MycroftAI/hardware-mycroft-mark-II/mark-II-Rpi-devkit/Reference Files/Switches/SLIDE.pdf

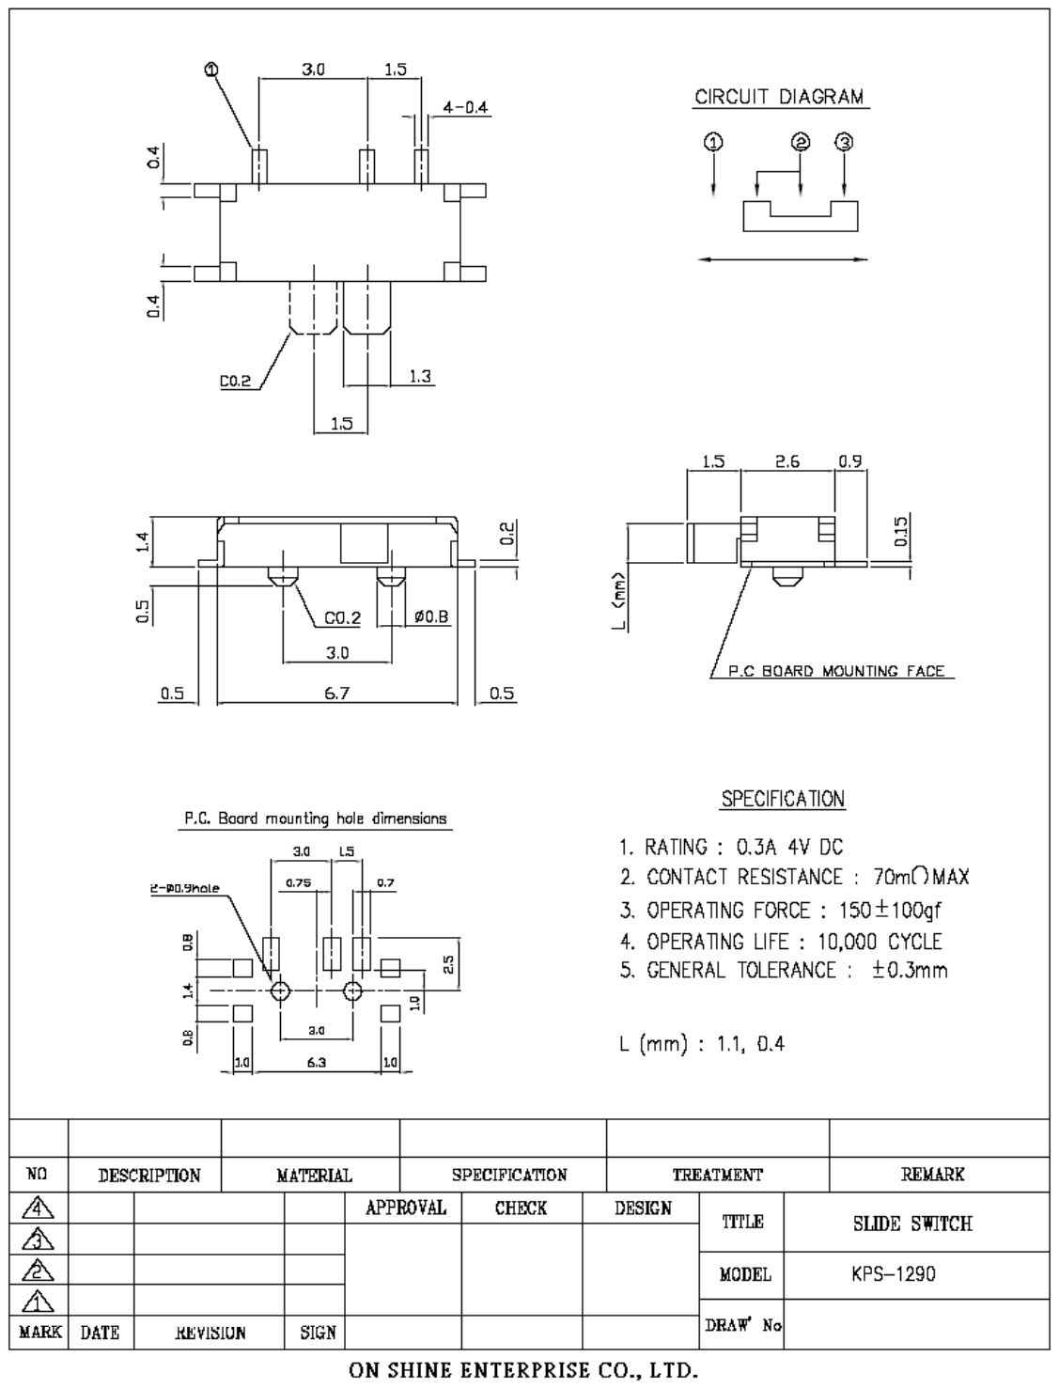
[picture p6: page 1]
