MycroftAI/hardware-mycroft-mark-II/mark-II-production/images/SJ-201-R10-back.png

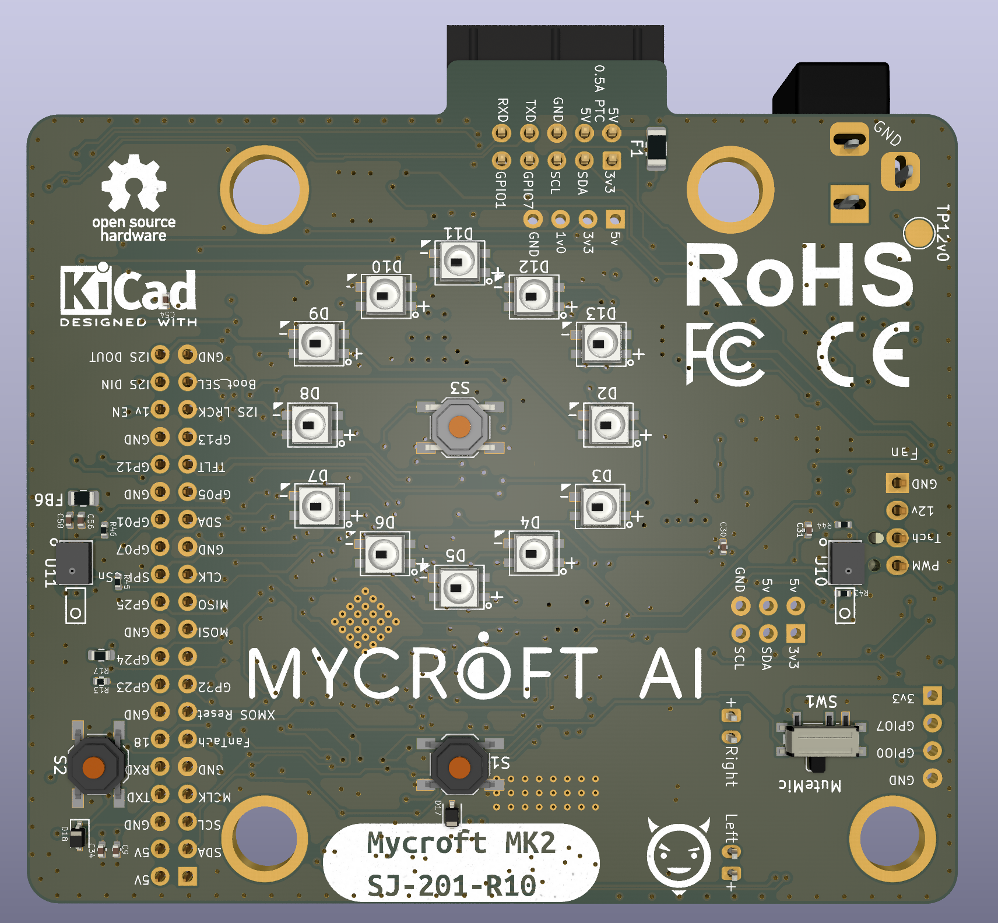
mark-II-production/images/SJ-201-R10-back.png
