MycroftAI/hardware-mycroft-mark-II/mark-II-Rpi-devkit/images/pcb-render-SJ-201-R4v11-front.png

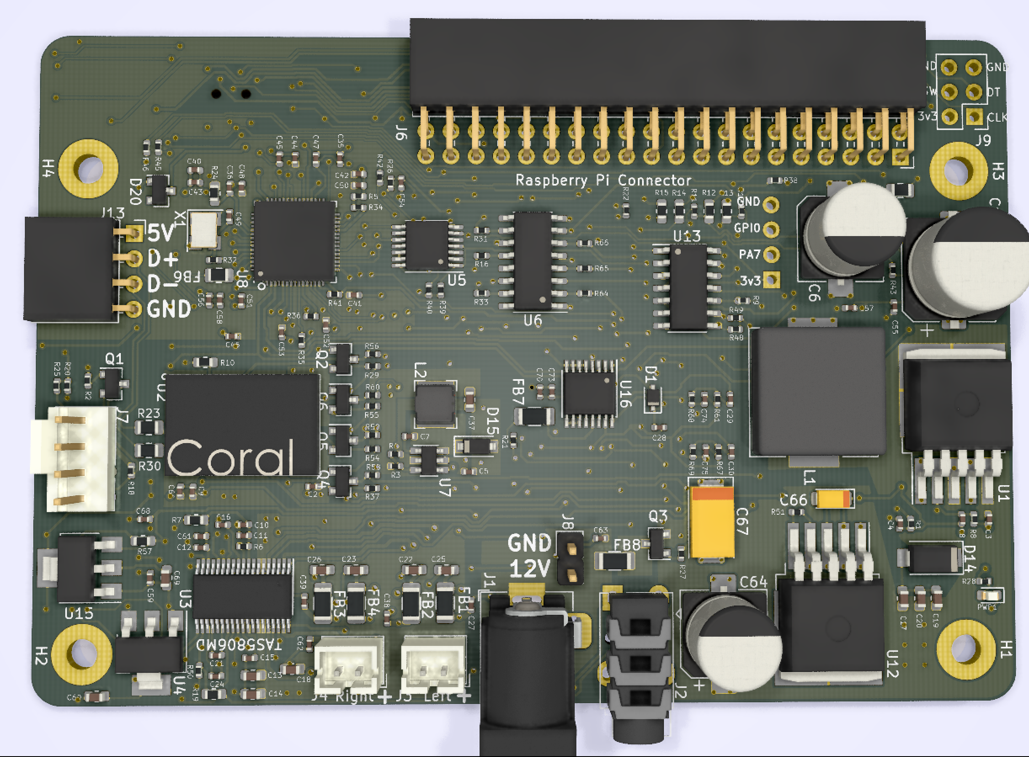
mark-II-Rpi-devkit/images/pcb-render-SJ-201-R4v11-front.png
