MycroftAI/hardware-mycroft-mark-II/mark-II-Rpi-devkit/images/pcb-render-v0.60-front.png

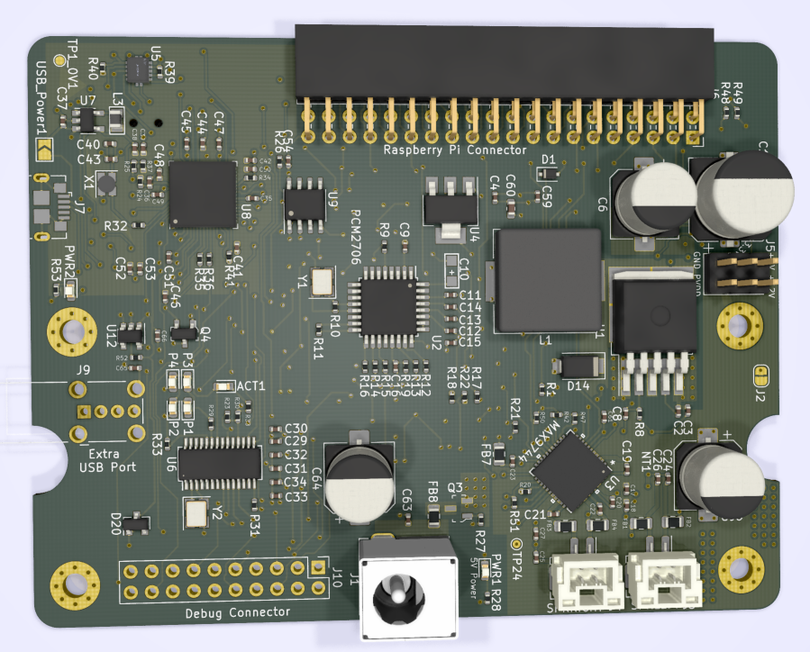
mark-II-Rpi-devkit/images/pcb-render-v0.60-front.png
