MycroftAI/hardware-mycroft-mark-II/mark-II-Rpi-devkit/images/pcb-render-v0.65-front.png

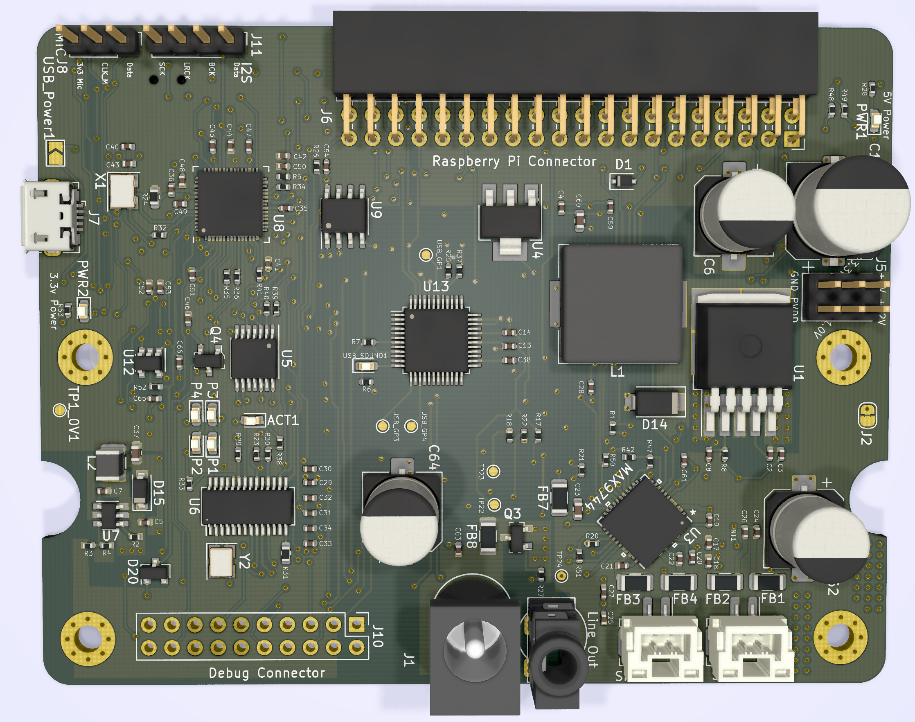
mark-II-Rpi-devkit/images/pcb-render-v0.65-front.png
