MycroftAI/hardware-mycroft-mark-II/mark-II-Rpi-devkit/images/pcb-render-v0.67c-back.png

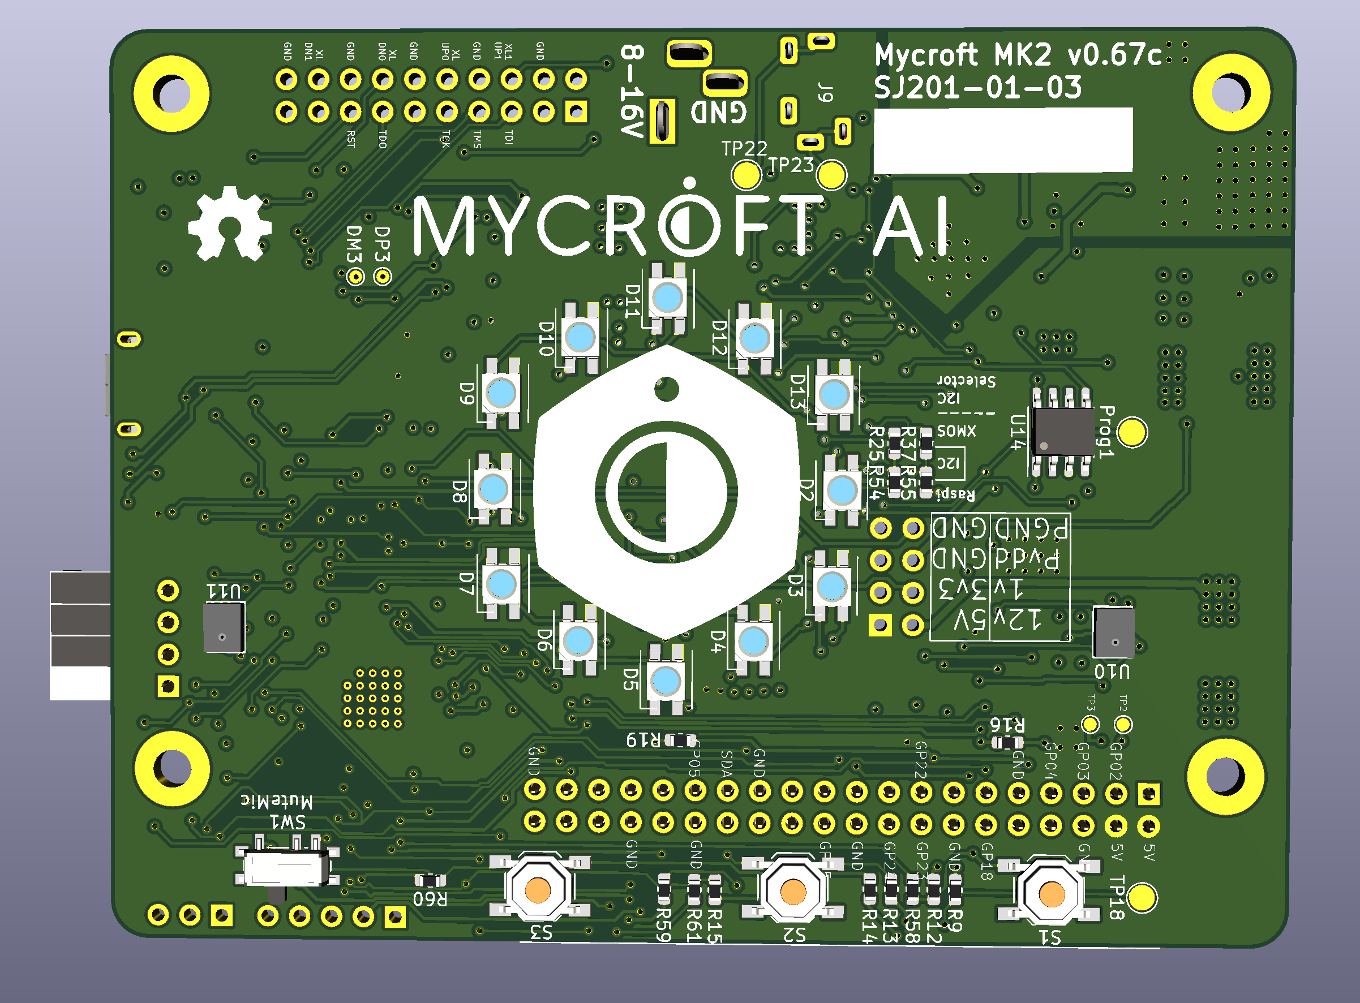
mark-II-Rpi-devkit/images/pcb-render-v0.67c-back.png
