MycroftAI/hardware-mycroft-mark-II/mark-II-Rpi-devkit/images/Sj-201-R4-how it started.png

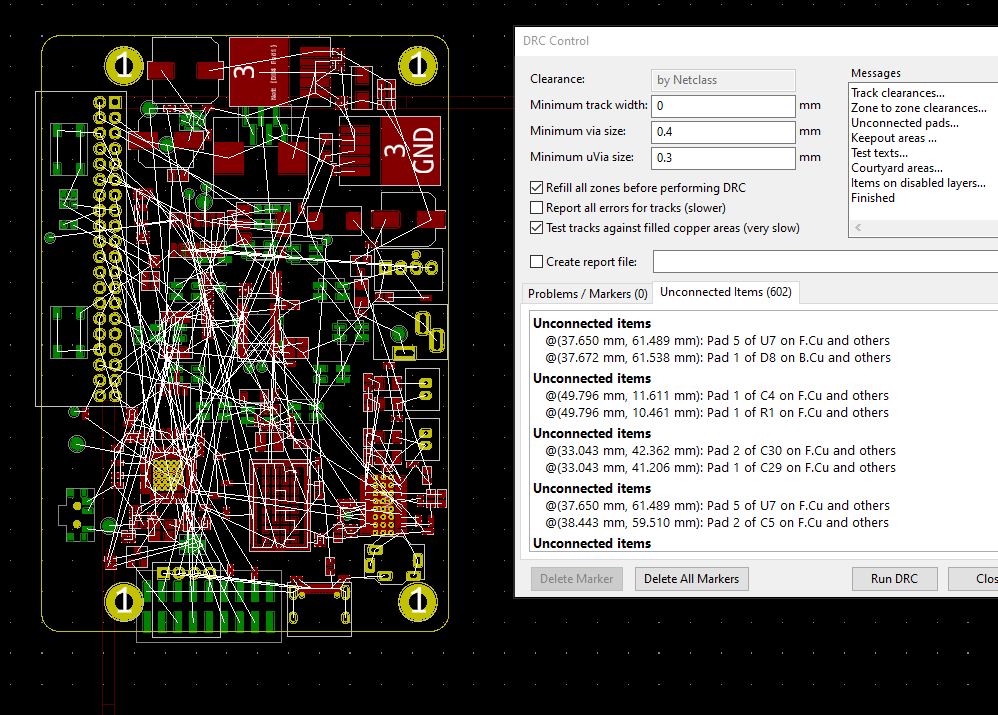
mark-II-Rpi-devkit/images/Sj-201-R4-how it started.png
