MycroftAI/hardware-mycroft-mark-II/mark-II-Rpi-devkit/images/SJ-202-USB-front.png

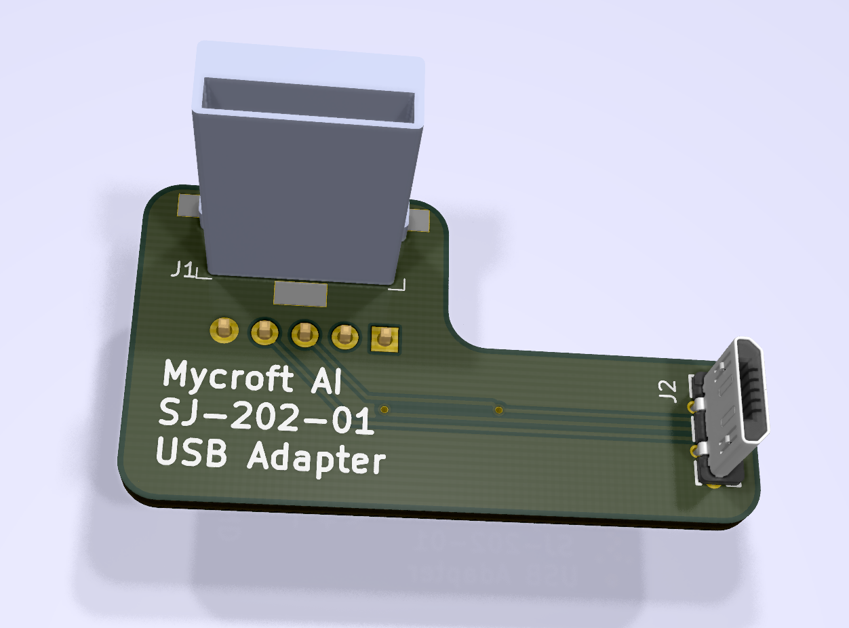
mark-II-Rpi-devkit/images/SJ-202-USB-front.png
