MycroftAI/hardware-mycroft-mark-II/mark-II-rpi-ots/CAD/threaded insert locations/Audio Chamber Back.png

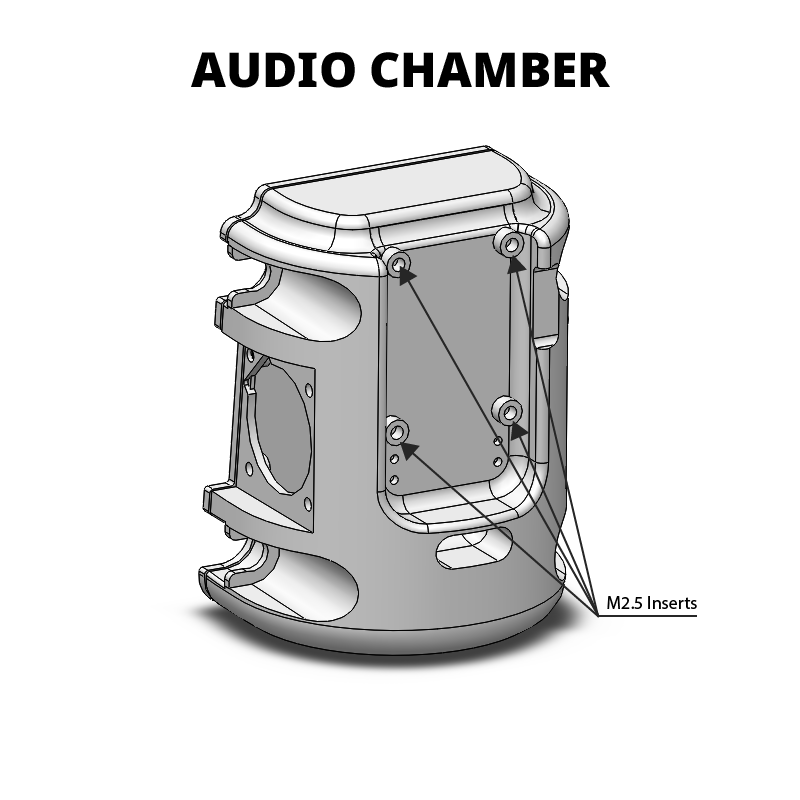
mark-II-rpi-ots/CAD/threaded insert locations/Audio Chamber Back.png
