MycroftAI/hardware-mycroft-mark-II/mark-II-rpi-ots/CAD/threaded insert locations/Audio Chamber Front.png

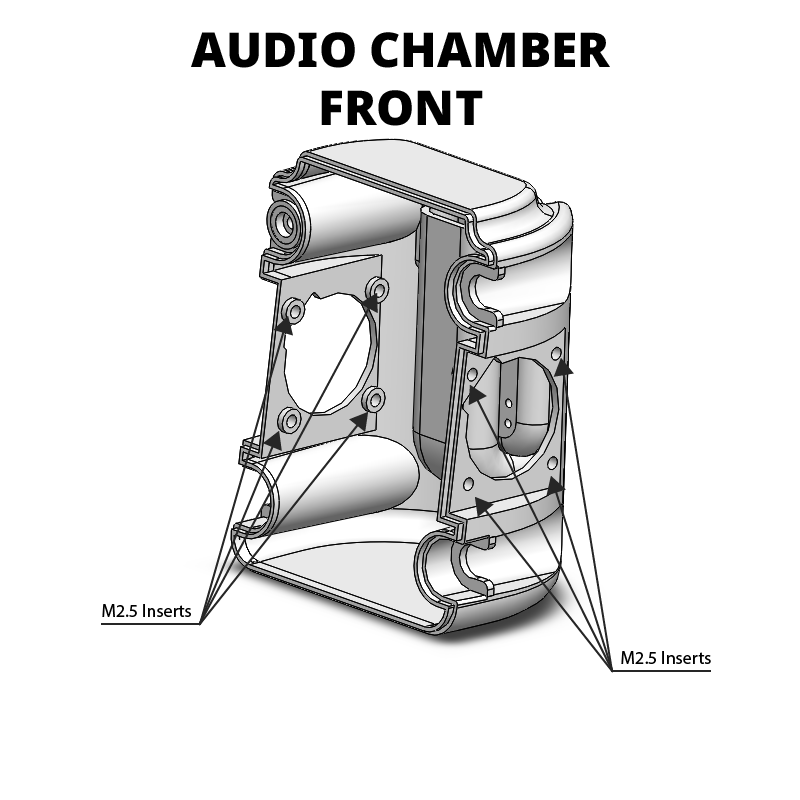
mark-II-rpi-ots/CAD/threaded insert locations/Audio Chamber Front.png
