MycroftAI/hardware-mycroft-mark-II/mark-II-rpi-ots/CAD/threaded insert locations/Base.png

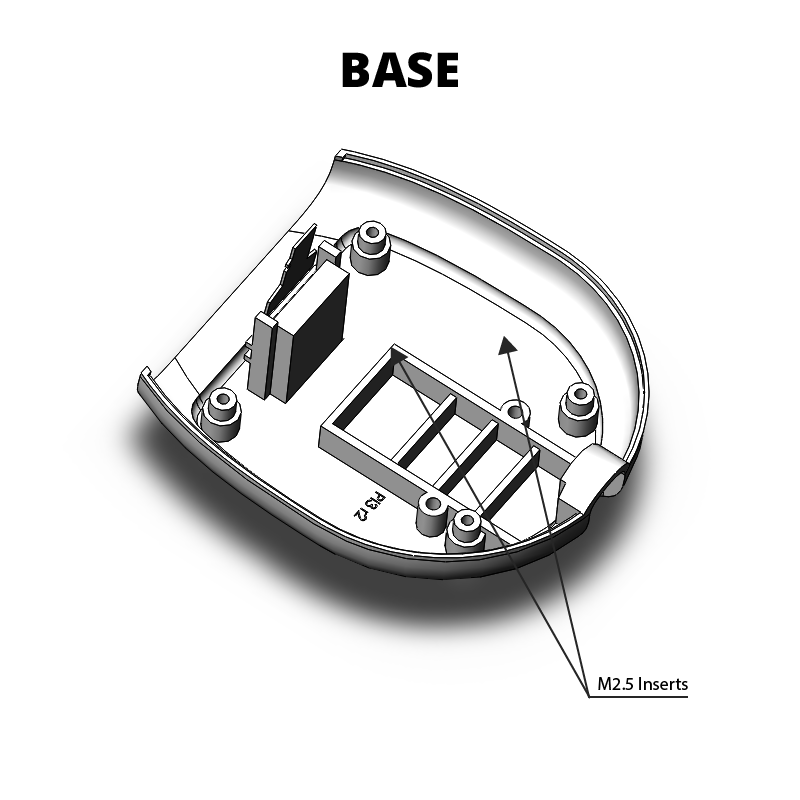
mark-II-rpi-ots/CAD/threaded insert locations/Base.png
