MycroftAI/hardware-mycroft-mark-II/mark-II-rpi-ots/CAD/threaded insert locations/Front.png

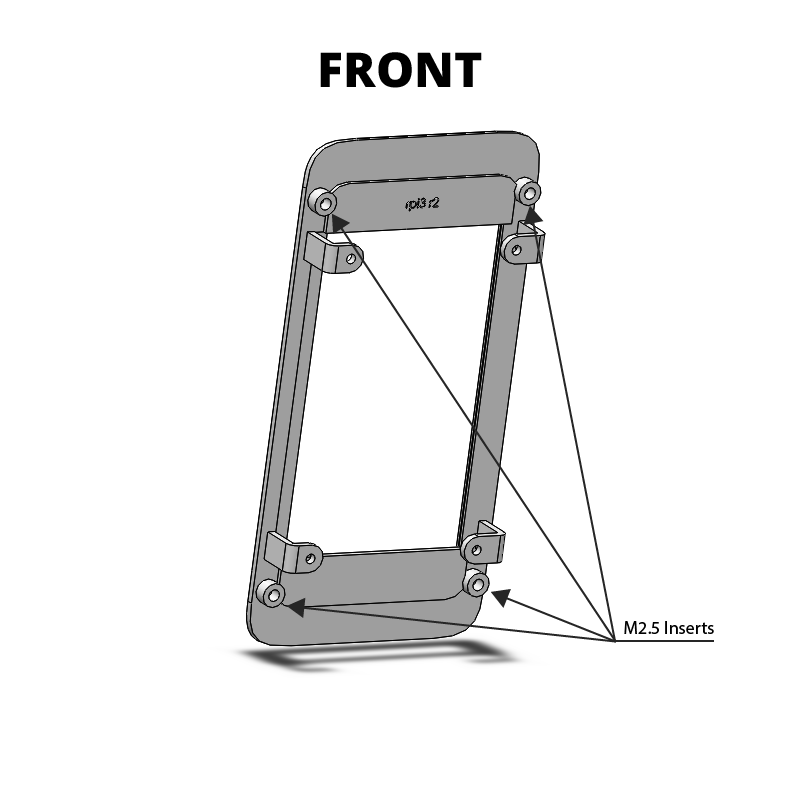
mark-II-rpi-ots/CAD/threaded insert locations/Front.png
