MycroftAI/hardware-mycroft-mark-II/mark-II-rpi-ots/CAD/threaded insert locations/Top-2.png

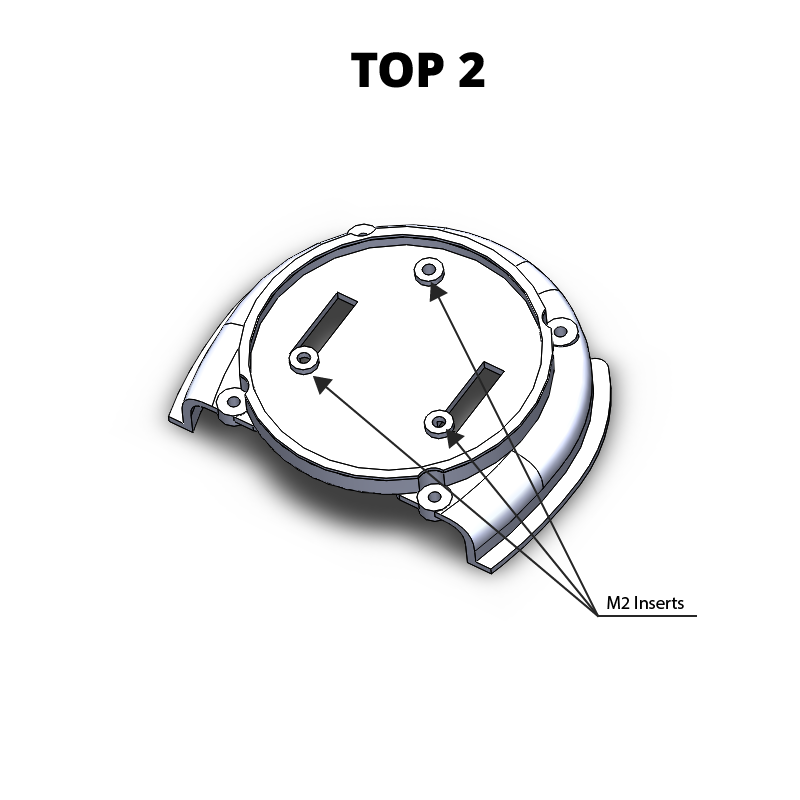
mark-II-rpi-ots/CAD/threaded insert locations/Top-2.png
