MycroftAI/hardware-mycroft-mark-II/mark-II-rpi-ots/CAD/threaded insert locations/Top.png

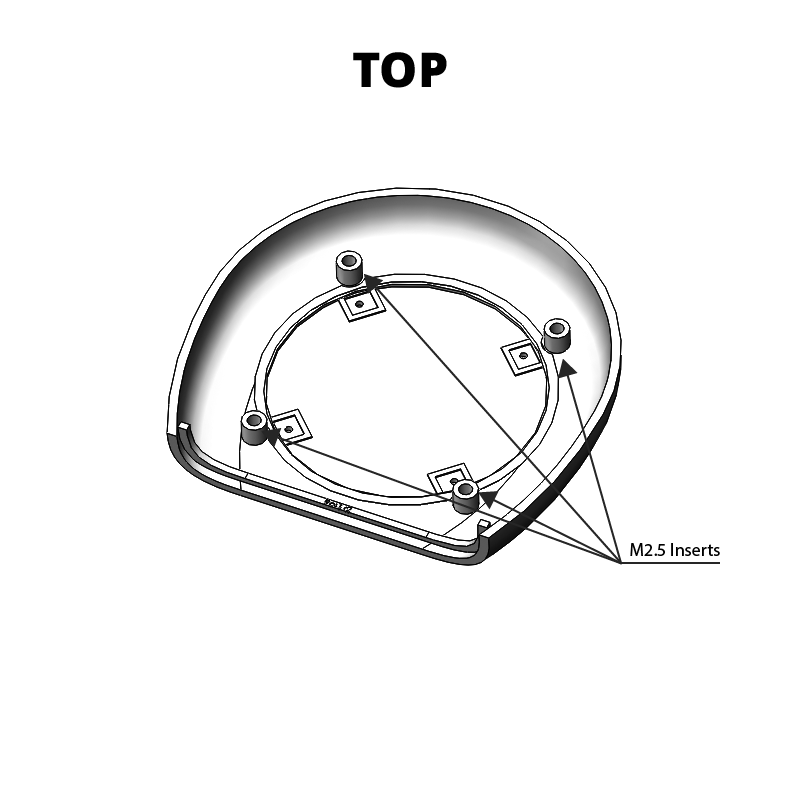
mark-II-rpi-ots/CAD/threaded insert locations/Top.png
