MycroftAI/hardware-mycroft-mark-II/mark-II-Rpi-devkit/Mechanical CAD/SJ240/MKII Camera Shutter 3 r9.stl

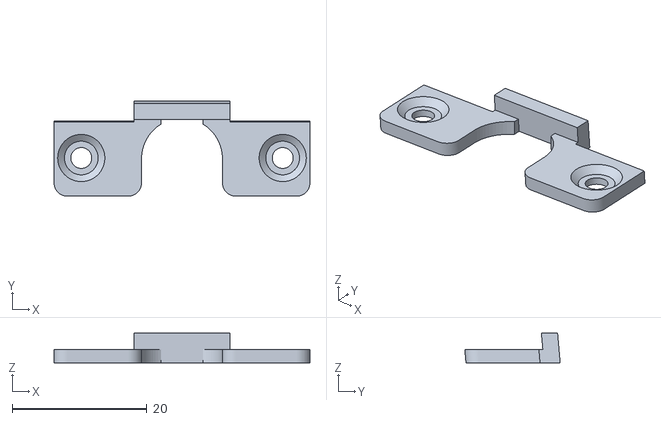
[picture p50: CAD file, 2021-03-14]
mark-II-Rpi-devkit/Mechanical CAD/SJ240/MKII Camera Shutter 3 r9.stl
38.0 x 14.2 x 4.41
