MycroftAI/hardware-mycroft-mark-II/mark-II-rpi-ots/CAD/STL/MIIr_AC_front_pi3_r2.1.STL

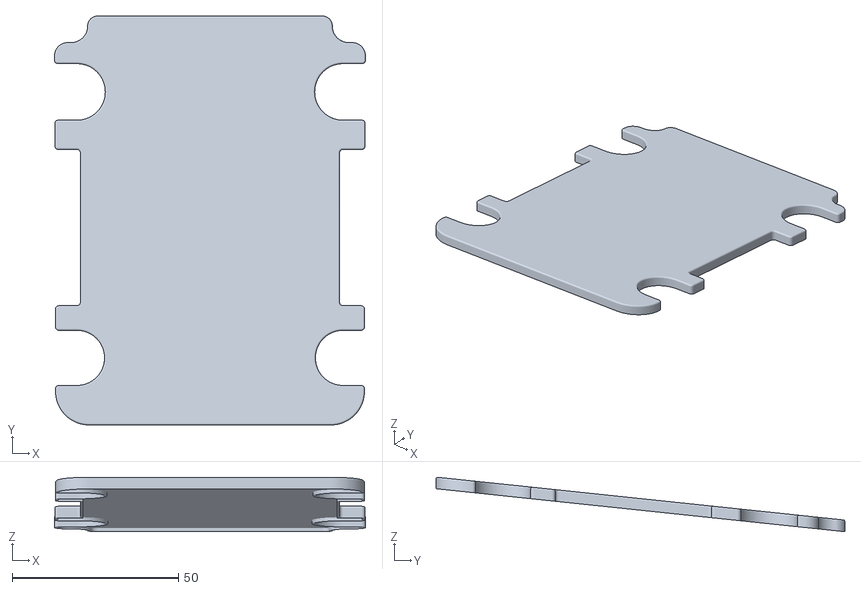
[picture p51: CAD file, 2020-01-30]
mark-II-rpi-ots/CAD/STL/MIIr_AC_front_pi3_r2.1.STL
93.5 x 123.0 x 16.4
