MycroftAI/hardware-mycroft-mark-II/mark-II-Rpi-devkit/Mechanical CAD/SJ240/MKII Camera Shutter 2 r9.stl

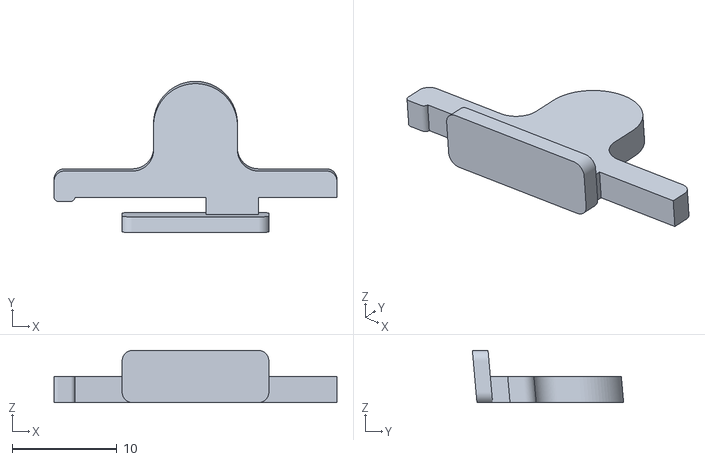
[picture p52: CAD file, 2021-03-14]
mark-II-Rpi-devkit/Mechanical CAD/SJ240/MKII Camera Shutter 2 r9.stl
27.0 x 14.4 x 4.98
