MycroftAI/hardware-mycroft-mark-II/mark-II-rpi-ots/CAD/STL/MIIr_base_pi3_r2.STL

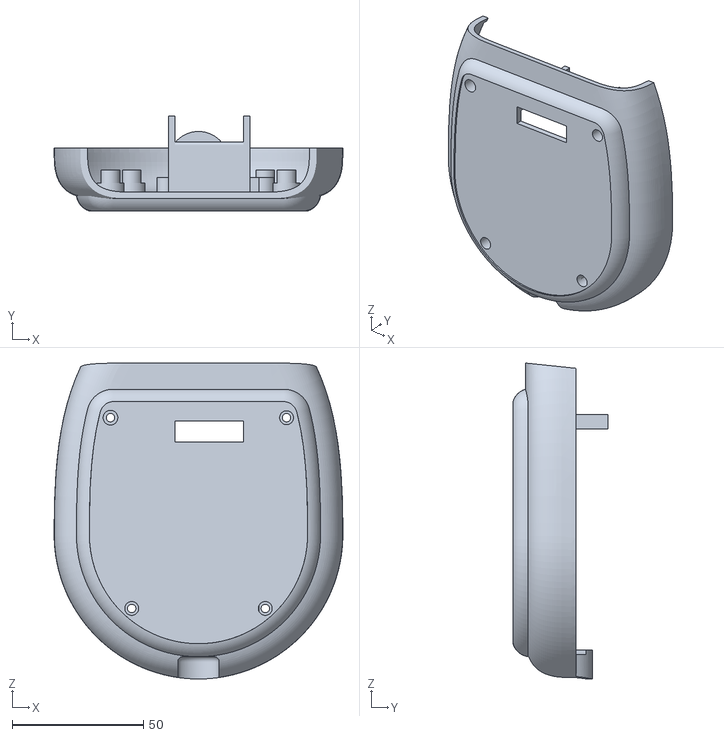
[picture p53: CAD file, 2020-01-30]
mark-II-rpi-ots/CAD/STL/MIIr_base_pi3_r2.STL
110.0 x 36.2 x 120.4
