MycroftAI/hardware-mycroft-mark-II/mark-II-Rpi-devkit/Mechanical CAD/SJ240/MKII Camera Shutter 1 r9.stl

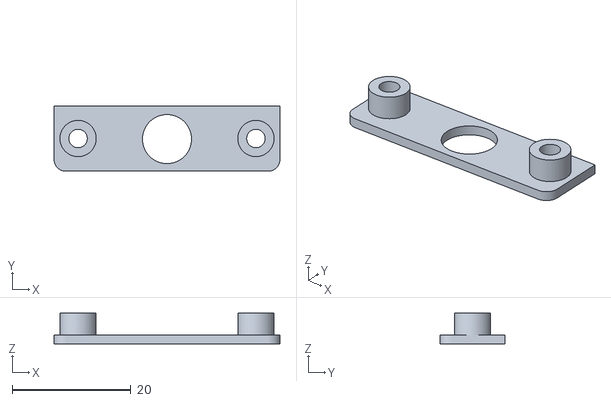
[picture p54: CAD file, 2021-03-14]
mark-II-Rpi-devkit/Mechanical CAD/SJ240/MKII Camera Shutter 1 r9.stl
38.0 x 11.0 x 5.14
