MycroftAI/hardware-mycroft-mark-II/mark-II-rpi-ots/CAD/STL/MIIr_back_bosses_pi3_r2.STL

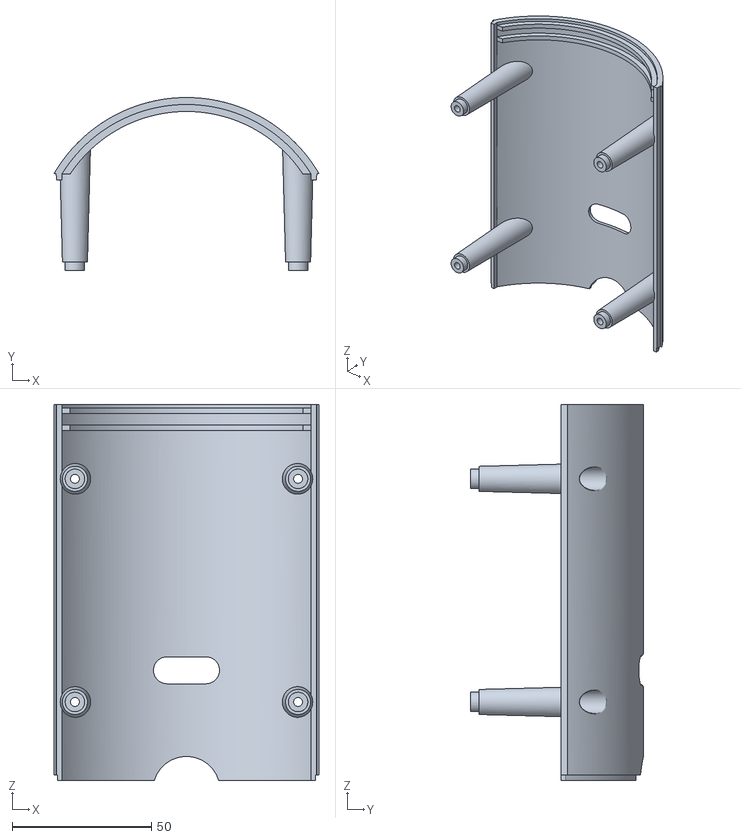
[picture p55: CAD file, 2020-01-20]
mark-II-rpi-ots/CAD/STL/MIIr_back_bosses_pi3_r2.STL
95.0 x 62.0 x 134.8
