MycroftAI/hardware-mycroft-mark-II/mark-II-Rpi-devkit/Mechanical CAD/SJ240/MKII switch r9.stl

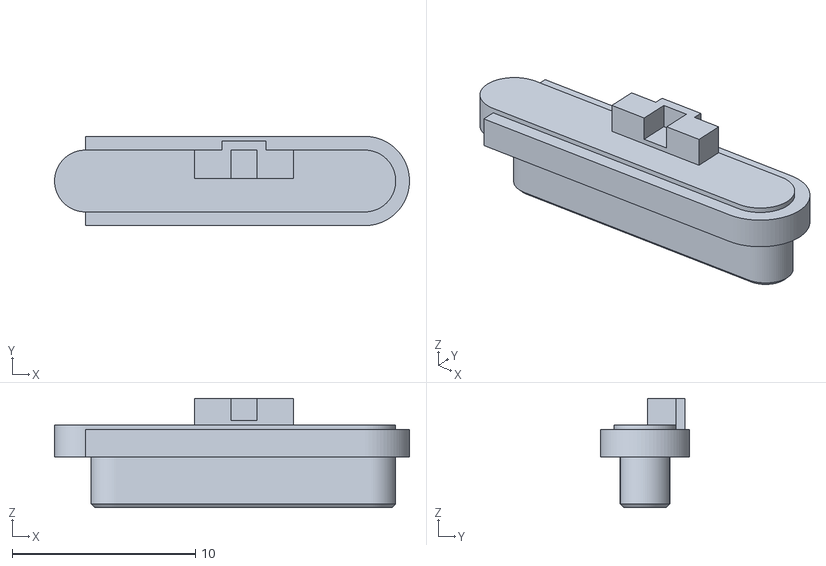
[picture p56: CAD file, 2021-03-14]
mark-II-Rpi-devkit/Mechanical CAD/SJ240/MKII switch r9.stl
19.4 x 4.87 x 5.96
