MycroftAI/hardware-mycroft-mark-II/mark-II-rpi-ots/CAD/STL/MIIr_front_plate_pi3_r2.STL

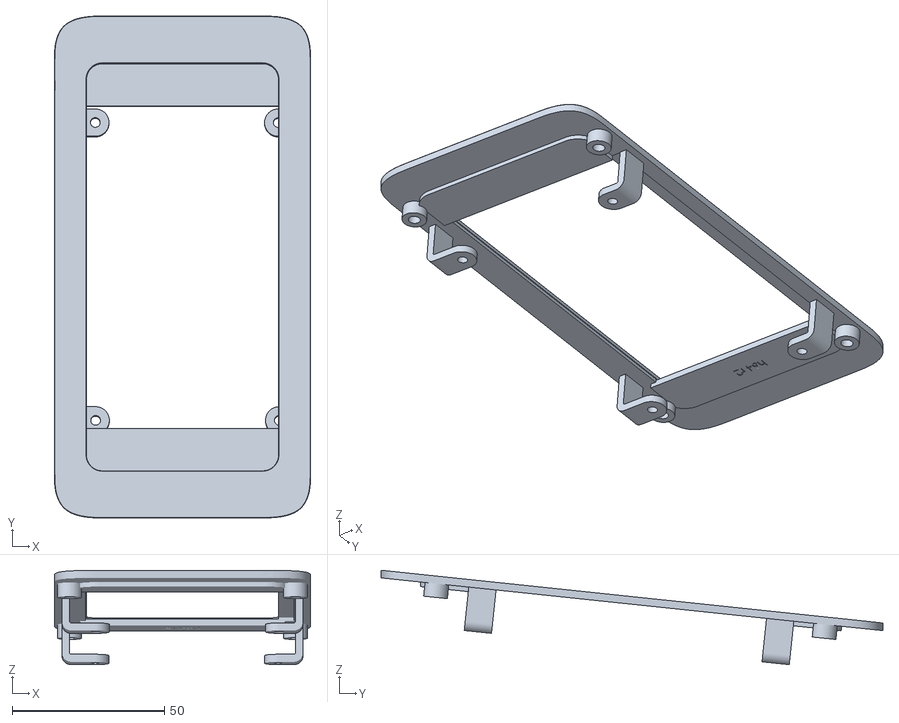
[picture p57: CAD file, 2020-01-20]
mark-II-rpi-ots/CAD/STL/MIIr_front_plate_pi3_r2.STL
84.0 x 164.6 x 30.9
