MycroftAI/hardware-mycroft-mark-II/mark-II-Rpi-devkit/Mechanical CAD/SJ240/MKII buttons r9.1.STL

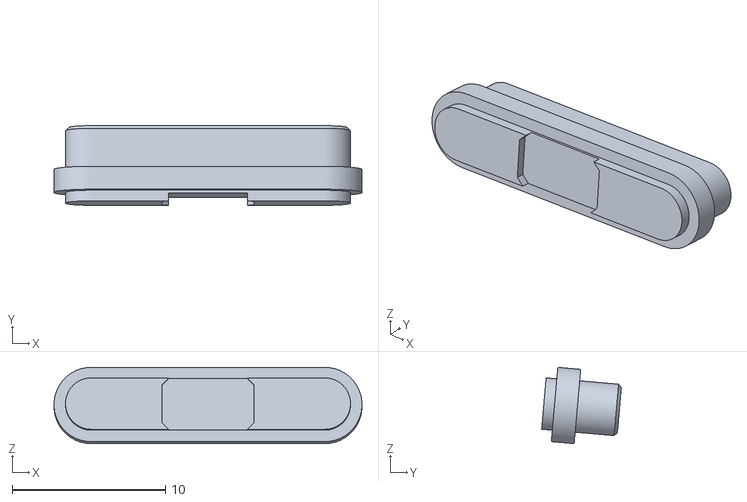
[picture p58: CAD file, 2021-03-14]
mark-II-Rpi-devkit/Mechanical CAD/SJ240/MKII buttons r9.1.STL
20.1 x 5.21 x 4.98
