MycroftAI/hardware-mycroft-mark-II/mark-II-Rpi-devkit/Mechanical CAD/SJ240/MKII Display Bezel R9.stl

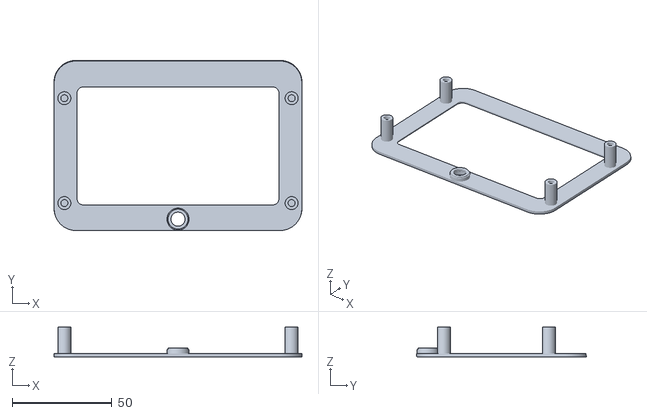
[picture p61: CAD file, 2021-03-12]
mark-II-Rpi-devkit/Mechanical CAD/SJ240/MKII Display Bezel R9.stl
124.1 x 85.1 x 14.9
