MycroftAI/hardware-mycroft-mark-II/mark-II-Rpi-devkit/Mechanical CAD/SJ240/MKII Display Housing r9.stl

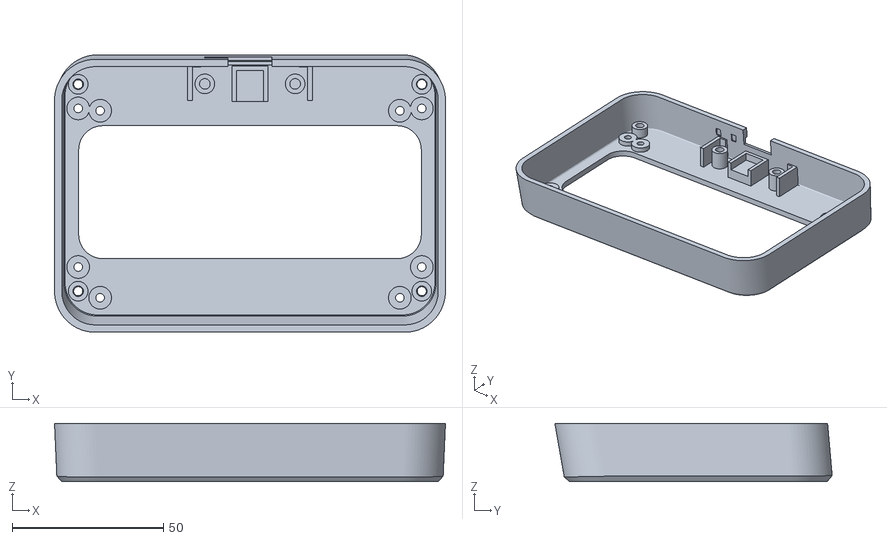
[picture p62: CAD file, 2021-03-12]
mark-II-Rpi-devkit/Mechanical CAD/SJ240/MKII Display Housing r9.stl
129.4 x 91.8 x 19.3
