MycroftAI/hardware-mycroft-mark-II/mark-II-Rpi-devkit/Mechanical CAD/SJ240/MKII Back r9.stl

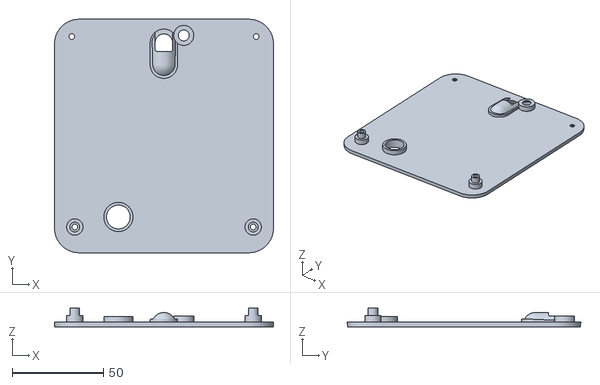
[picture p63: CAD file, 2021-03-12]
mark-II-Rpi-devkit/Mechanical CAD/SJ240/MKII Back r9.stl
120.0 x 128.0 x 10.2
