MycroftAI/hardware-mycroft-mark-II/mark-II-Rpi-devkit/Mechanical CAD/SJ240/MKII Grill r9.stl

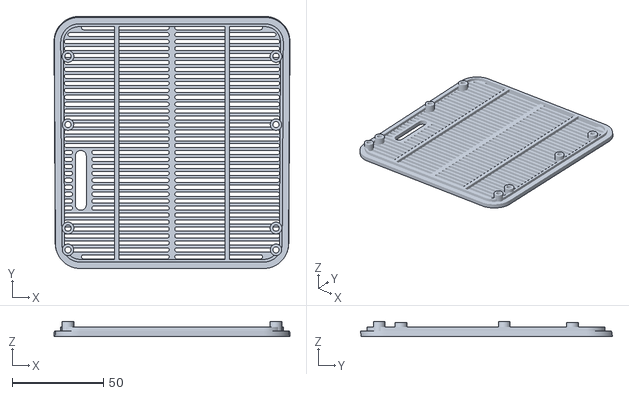
[picture p64: CAD file, 2021-03-12]
mark-II-Rpi-devkit/Mechanical CAD/SJ240/MKII Grill r9.stl
129.0 x 137.8 x 8.00
