MycroftAI/hardware-mycroft-mark-II/mark-II-Rpi-devkit/Mechanical CAD/SJ240/MKII Audio Chamber r9.stl

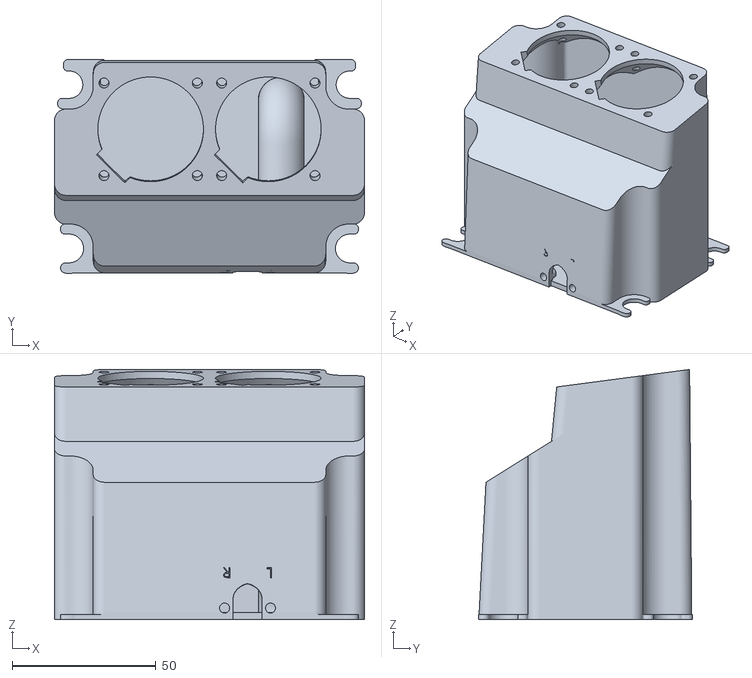
[picture p65: CAD file, 2021-03-12]
mark-II-Rpi-devkit/Mechanical CAD/SJ240/MKII Audio Chamber r9.stl
108.0 x 74.5 x 87.1
