MycroftAI/hardware-mycroft-mark-II/mark-II-production/assembly-instructions/images/display02.jpeg

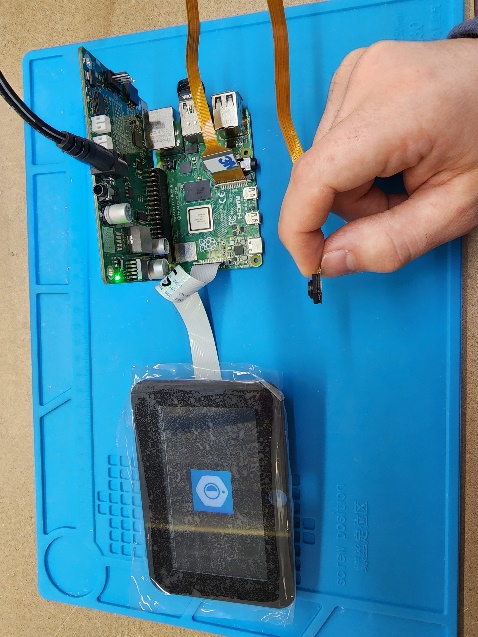
mark-II-production/assembly-instructions/images/display02.jpeg
