MycroftAI/hardware-mycroft-mark-II/mark-II-Rpi-devkit/images/JLC 0.65a-front assembly.png

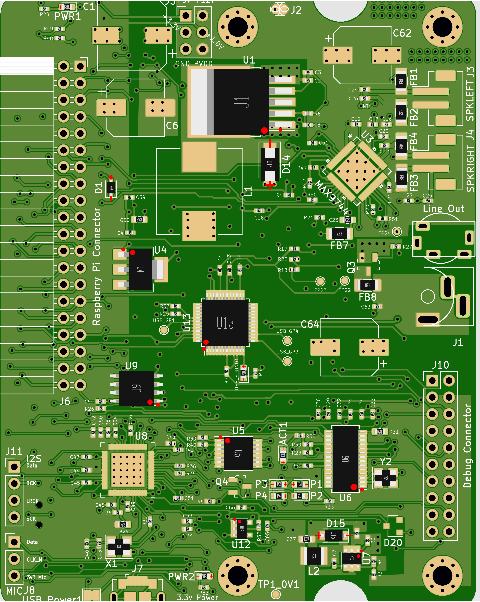
mark-II-Rpi-devkit/images/JLC 0.65a-front assembly.png
