MycroftAI/hardware-mycroft-mark-II/mark-II-production/AudioAmp.kicad_sch

## KiCad design mark-II-production/AudioAmp.kicad_sch (2022-10-22)

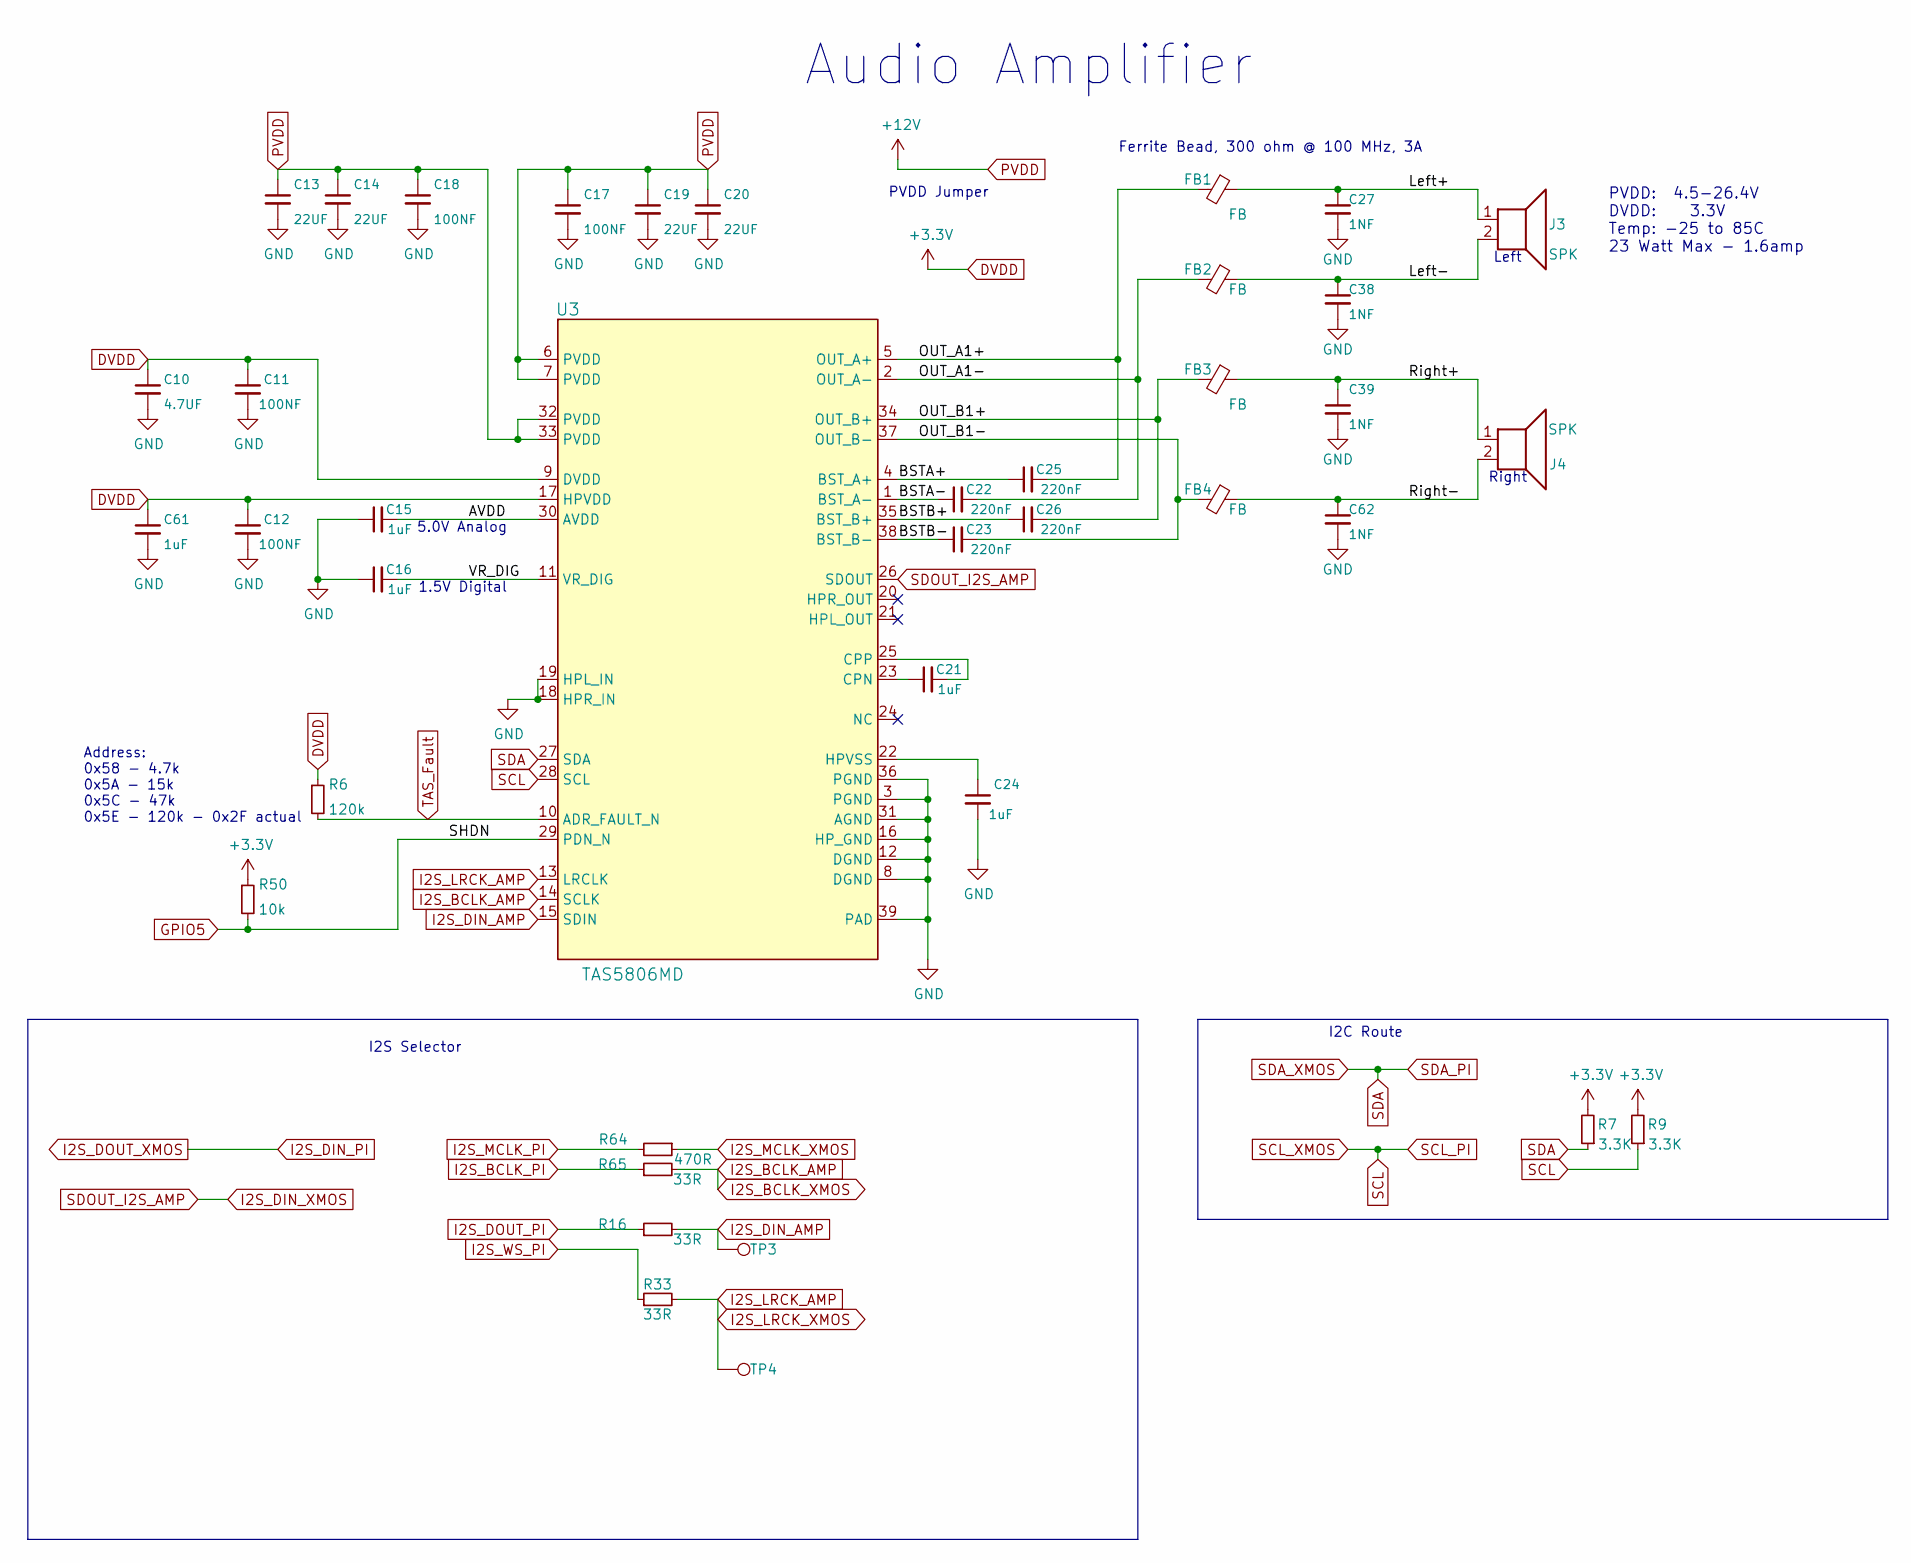
[picture p143: schematic AudioAmp.kicad_sch]

Parts:
C10: 4.7UF; C_0402_1005Metric; MPN CL05A475MP5NRNC; LCSC C23733
C11, C12: 100NF; C_0402_1005Metric; MPN CC0402KRX7R8BB104; LCSC C1525
C13, C14, C19, C20: 22UF; C_0603_1608Metric; MPN CL10A226MQ8NRNC; LCSC C59461
C15, C16, C21, C24, C61: 1uF; C_0402_1005Metric; MPN CL05A105KA5NQNC; LCSC C52923
C17, C18: 100NF; C_0603_1608Metric; MPN CC0603KRX7R9BB104; LCSC C14663
C22, C23, C25, C26: 220nF; C_0603_1608Metric; MPN CL10B224KA8NNNC; LCSC C21120
C27, C38, C39, C62: 1NF; C_0402_1005Metric; MPN 0402B102K500NT; LCSC C1523
FB1, FB2, FB3, FB4: FB; R_1206_3216Metric; MPN MLB3216-301P3A(f); LCSC C29107
J3, J4: SPK; JST_PH_B2B-PH-K_1x02_P2.00mm_Vertical; MPN B2B-PH-K-S(LF)(SN); LCSC C131337
R6: 120k; R_0402_1005Metric; MPN 0402WGF1203TCE; LCSC C25750
R7, R9: 3.3K; R_0402_1005Metric; MPN 0402WGF3301TCE; LCSC C25890
R16, R33, R65: 33R; R_0402_1005Metric; MPN 0402WGF330JTCE; LCSC C25105
R50: 10k; R_0402_1005Metric; MPN RC0402FR-0710KL; LCSC C25744
R64: 470R; R_0603_1608Metric; MPN 0603WAF4700T5E; LCSC C23179
TP3, TP4: TestPoint; TestPoint_Pad_D1.0mm; MPN DNP
U3: TAS5806MD; TAS5806MDDCPR; MPN TAS5806MDDCPR

Connections:
+3.3V: C10.1, C11.1, C12.1, C61.1, R6.1, R7.2, R9.2, R50.1, U3.9 (DVDD), U3.17 (HPVDD)
+12V: C13.1, C14.1, C17.1, C18.1, C19.1, C20.1, U3.6 (PVDD), U3.7 (PVDD), U3.32 (PVDD), U3.33 (PVDD)
AVDD: C15.2, U3.30 (AVDD)
BSTA+: C25.1, U3.4 (BST_A+)
BSTA-: C22.1, U3.1 (BST_A-)
BSTB+: C26.1, U3.35 (BST_B+)
BSTB-: C23.1, U3.38 (BST_B-)
GND: C10.2, C11.2, C12.2, C13.2, C14.2, C15.1, C16.1, C17.2, C18.2, C19.2, C20.2, C24.2, C27.2, C38.2, C39.2, C61.2, C62.2, U3.3 (PGND), U3.8 (DGND), U3.12 (DGND), U3.16 (HP_GND), U3.18 (HPR_IN), U3.19 (HPL_IN), U3.31 (AGND), U3.36 (PGND), U3.39 (PAD)
GPIO5: R50.2, U3.29 (PDN_N)
I2S_BCLK_AMP: R65.2, U3.14 (SCLK)
I2S_BCLK_PI: R65.1
I2S_DIN_AMP: R16.2, TP3.1, U3.15 (SDIN)
I2S_DIN_XMOS: U3.26 (SDOUT)
I2S_DOUT_PI: R16.1
I2S_LRCK_AMP: R33.2, TP4.1, U3.13 (LRCLK)
I2S_MCLK_PI: R64.2
I2S_MCLK_XMOS: R64.1
I2S_WS_PI: R33.1
Left+: C27.1, FB1.1, J3.1
Left-: C38.1, FB2.1, J3.2
unnamed: C21.1, U3.23 (CPN)
unnamed: C21.2, U3.25 (CPP)
unnamed: C24.1, U3.22 (HPVSS)
OUT_A1+: C25.2, FB1.2, U3.5 (OUT_A+)
OUT_A1-: C22.2, FB2.2, U3.2 (OUT_A-)
OUT_B1+: C26.2, FB3.2, U3.34 (OUT_B+)
OUT_B1-: C23.2, FB4.2, U3.37 (OUT_B-)
Right+: C39.1, FB3.1, J4.1
Right-: C62.1, FB4.1, J4.2
SCL: R9.1, U3.28 (SCL)
SDA: R7.1, U3.27 (SDA)
TAS_Fault: R6.2, U3.10 (ADR_FAULT_N)
VR_DIG: C16.2, U3.11 (VR_DIG)

Notes on the sheet:
1.5V Digital
I2C Route
Ferrite Bead, 300 ohm @ 100 MHz, 3A
5.0V Analog
PVDD Jumper
Address: 0x58 - 4.7k 0x5A - 15k 0x5C - 47k 0x5E - 120k - 0x2F actual
Right
Audio Amplifier
Left
PVDD: 4.5-26.4V DVDD: 3.3V Temp: -25 to 85C 23 Watt Max - 1.6amp
I2S Selector
