MycroftAI/hardware-mycroft-mark-II/mark-II-production/MCU.kicad_sch

## KiCad design mark-II-production/MCU.kicad_sch (2022-10-22)

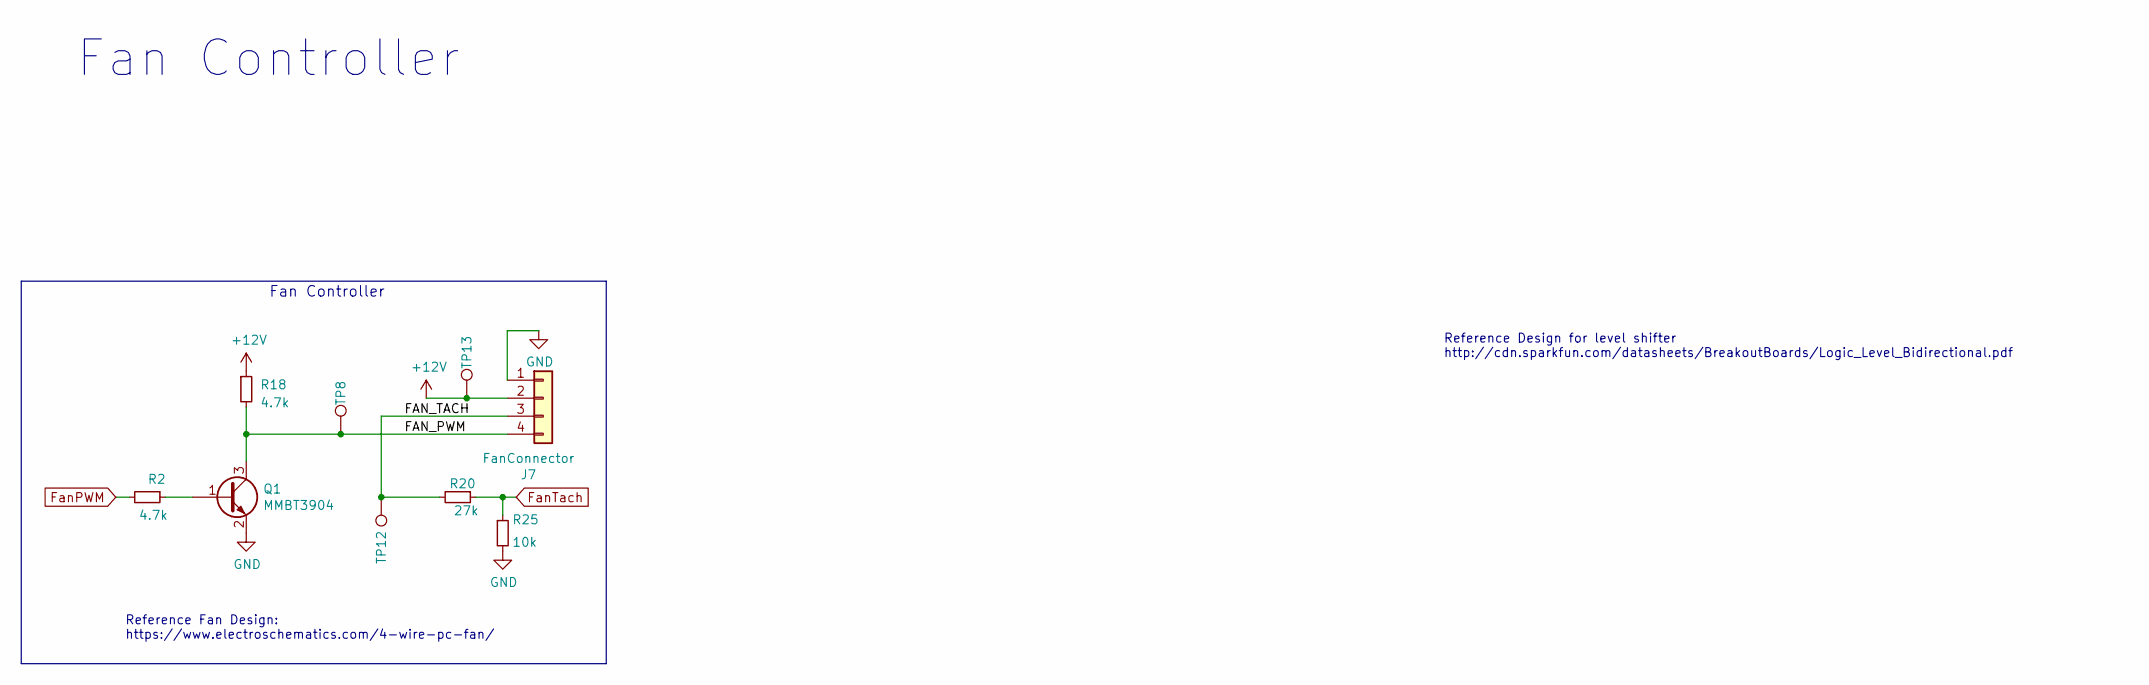
[picture p144: schematic MCU.kicad_sch]

Parts:
J7: FanConnector; FanPinHeader_1x04_P2.54mm_Vertical; MPN 744-81-04TG1B; LCSC C402775
Q1: MMBT3904; SOT-23; MPN MMBT3904; LCSC C382281
R2, R18: 4.7k; R_0402_1005Metric; MPN 0402WGF4701TCE; LCSC C25900
R20: 27k; R_0402_1005Metric; MPN 0402WGF2702TCE; LCSC C25771
R25: 10k; R_0402_1005Metric; MPN RC0402FR-0710KL; LCSC C25744
TP8, TP12, TP13: TestPoint; TestPoint_Pad_D1.0mm; MPN DNP

Connections:
+12V: J7.2, R18.1, TP13.1
FAN_PWM: J7.4, Q1.3 (C), R18.2, TP8.1
FAN_TACH: J7.3, R20.2, TP12.1
FanPWM: R2.2
FanTach: R20.1, R25.1
GND: J7.1, Q1.2 (E), R25.2
unnamed: Q1.1 (B), R2.1

Notes on the sheet:
Fan Controller
Reference Fan Design: https://www.electroschematics.com/4-wire-pc-fan/
Reference Design for level shifter http://cdn.sparkfun.com/datasheets/BreakoutBoards/Logic_Level_Bidirectional.pdf
