MycroftAI/hardware-mycroft-mark-II/mark-II-production/Power.kicad_sch

## KiCad design mark-II-production/Power.kicad_sch (2022-10-22)

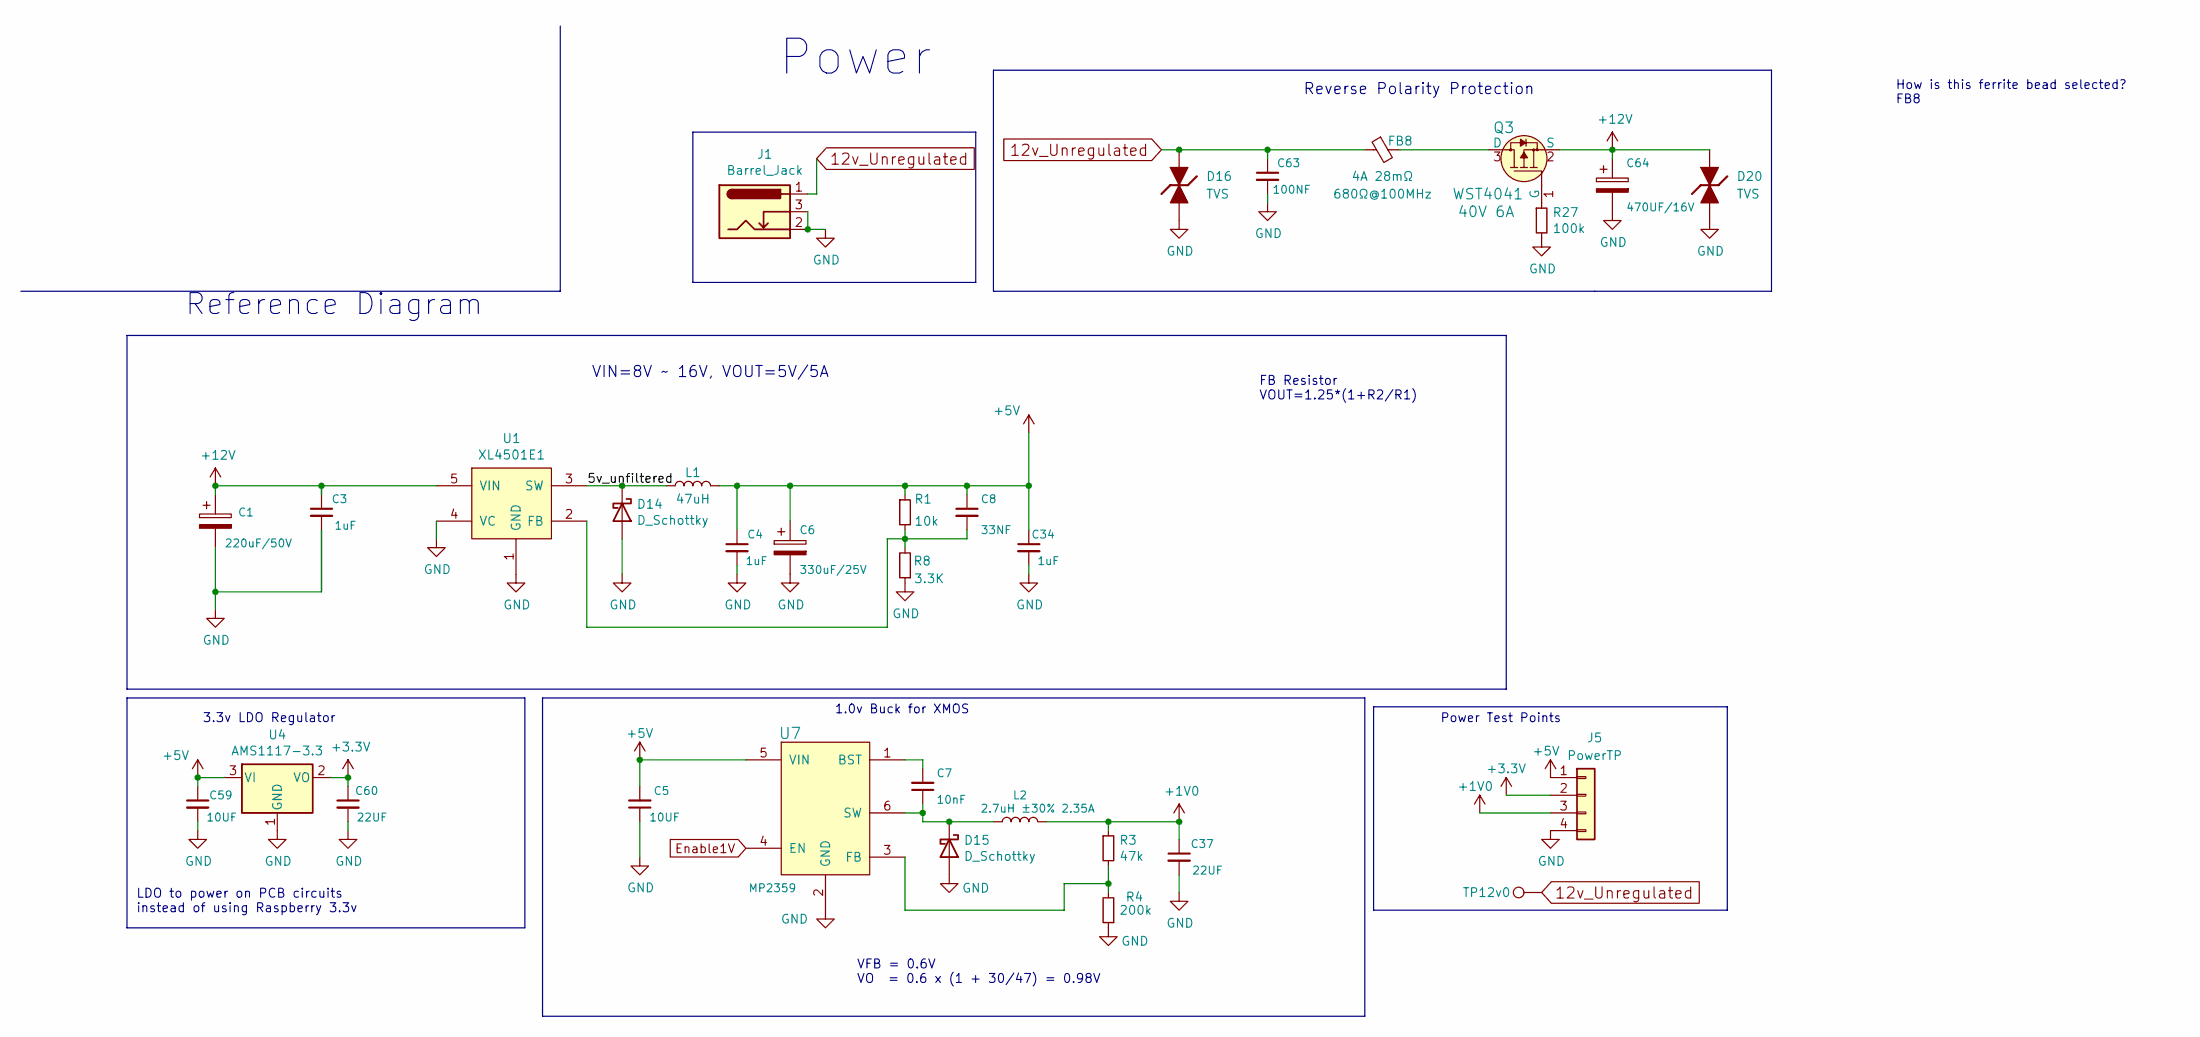
[picture p145: schematic Power.kicad_sch]

Parts:
C1: 220uF/50V; CP_Elec_10x10; MPN VE-221M1HTR-1010; LCSC C134732
C3, C4, C34: 1uF; C_0402_1005Metric; MPN CL05A105KA5NQNC; LCSC C52923
C5, C59: 10UF; C_0402_1005Metric; MPN CC0402MRX5R5BB106; LCSC C15525
C6: 330uF/25V; CP_Elec_8x10.5; MPN RVT1E331M0810; LCSC C286135
C7: 10nF; C_0402_1005Metric; MPN CL05B103KB5NNNC; LCSC C15195
C8: 33NF; C_0402_1005Metric; MPN GRM155R71A333KA01D; LCSC C1585
C37, C60: 22UF; C_0603_1608Metric; MPN CL10A226MQ8NRNE; LCSC C59461
C63: 100NF; C_0402_1005Metric; MPN CC0402KRX7R8BB104; LCSC C1525
C64: 470UF/16V; CP_Elec_8x10.5; MPN SMD CAP Aluminum 470uF-16V;D8.0*H10.2mm; LCSC C176671
D14: D_Schottky; D_SMA; MPN SS54F; LCSC C22452
D15: D_Schottky; D_SOD-123; MPN B5819W; LCSC C8598
D16, D20: TVS; D_SMB; LCSC C78408
FB8: 4A 28mΩ; R_1812_4532Metric; MPN FBMH4532HM681-T; LCSC C92881
J1: Barrel_Jack; BarrelJack_Horizontal; MPN DC-005-5A-2.0; LCSC C381116
J5: PowerTP; PinHeader_1x04_P2.54mm_Vertical; MPN DNP; LCSC DNP
L1: 47uH; L_Wuerth_HCI-1365; MPN YSPI1365-470M; LCSC C497913
L2: 2.7uH ±30% 2.35A; L_Bourns-SRN4018; MPN SRR4028-2R7Y
Q3: WST4041; SOT-23; MPN WST4041; LCSC C148357
R1: 10k; R_0402_1005Metric; MPN RC0402FR-0710KL; LCSC C25744
R3: 47k; R_0402_1005Metric; MPN 0402WGF4702TCE; LCSC C25792
R4: 200k; R_0402_1005Metric; MPN 0402WGF2003TCE; LCSC C25764
R8: 3.3K; R_0402_1005Metric; MPN 0402WGF3301TCE; LCSC C25890
R27: 100k; R_0402_1005Metric; MPN RC0402JR-07100KL; LCSC C25741
TP12v0: TestPoint; TestPoint_Pad_D2.5mm; MPN DNP
U1: XL4501E1; TO-263-5_TabPin3; MPN XL4501E1; LCSC C73025
U4: AMS1117-3.3; SOT-223-3_TabPin2; MPN AMS1117-3.3; LCSC C6186
U7: MP2359; TSOT-23-6; MPN MP2359DJ-LF-Z; LCSC C14259

Connections:
5v_unfiltered: D14.1 (K), L1.1, U1.3 (SW)
12v_Unregulated: C63.1, D16.1, FB8.1, J1.1, TP12v0.1
+1V0: C37.1, J5.3, L2.2, R3.1
+3.3V: C60.1, J5.2, U4.2 (VO)
+5V: C4.1, C5.2, C6.1, C8.1, C34.1, C59.1, J5.1, L1.2, R1.1, U4.3 (VI), U7.5 (VIN)
+12V: C1.1, C3.1, C64.1, D20.1, Q3.2 (S), U1.5 (VIN)
Enable1V: U7.4 (EN)
GND: C1.2, C3.2, C4.2, C5.1, C6.2, C34.2, C37.2, C59.2, C60.2, C63.2, C64.2, D14.2 (A), D15.2 (A), D16.2, D20.2, J1.2, J1.3, J5.4, R4.1, R8.1, R27.2, U1.1 (GND), U1.4 (VC), U4.1 (GND), U7.2 (GND)
unnamed: C7.1, D15.1 (K), L2.1, U7.6 (SW)
unnamed: C7.2, U7.1 (BST)
unnamed: C8.2, R1.2, R8.2, U1.2 (FB)
unnamed: FB8.2, Q3.3 (D)
unnamed: Q3.1 (G), R27.1
unnamed: R3.2, R4.2, U7.3 (FB)

Notes on the sheet:
Reference Diagram
LDO to power on PCB circuits instead of using Raspberry 3.3v
VIN=8V ~ 16V, VOUT=5V/5A
Power
VFB = 0.6V VO = 0.6 x (1 + 30/47) = 0.98V
Reverse Polarity Protection
1.0v Buck for XMOS
3.3v LDO Regulator
FB Resistor VOUT=1.25*(1+R2/R1)
How is this ferrite bead selected? FB8
Power Test Points
