MycroftAI/hardware-mycroft-mark-II/mark-II-production/RaspberryPi.kicad_sch

## KiCad design mark-II-production/RaspberryPi.kicad_sch (2022-10-22)

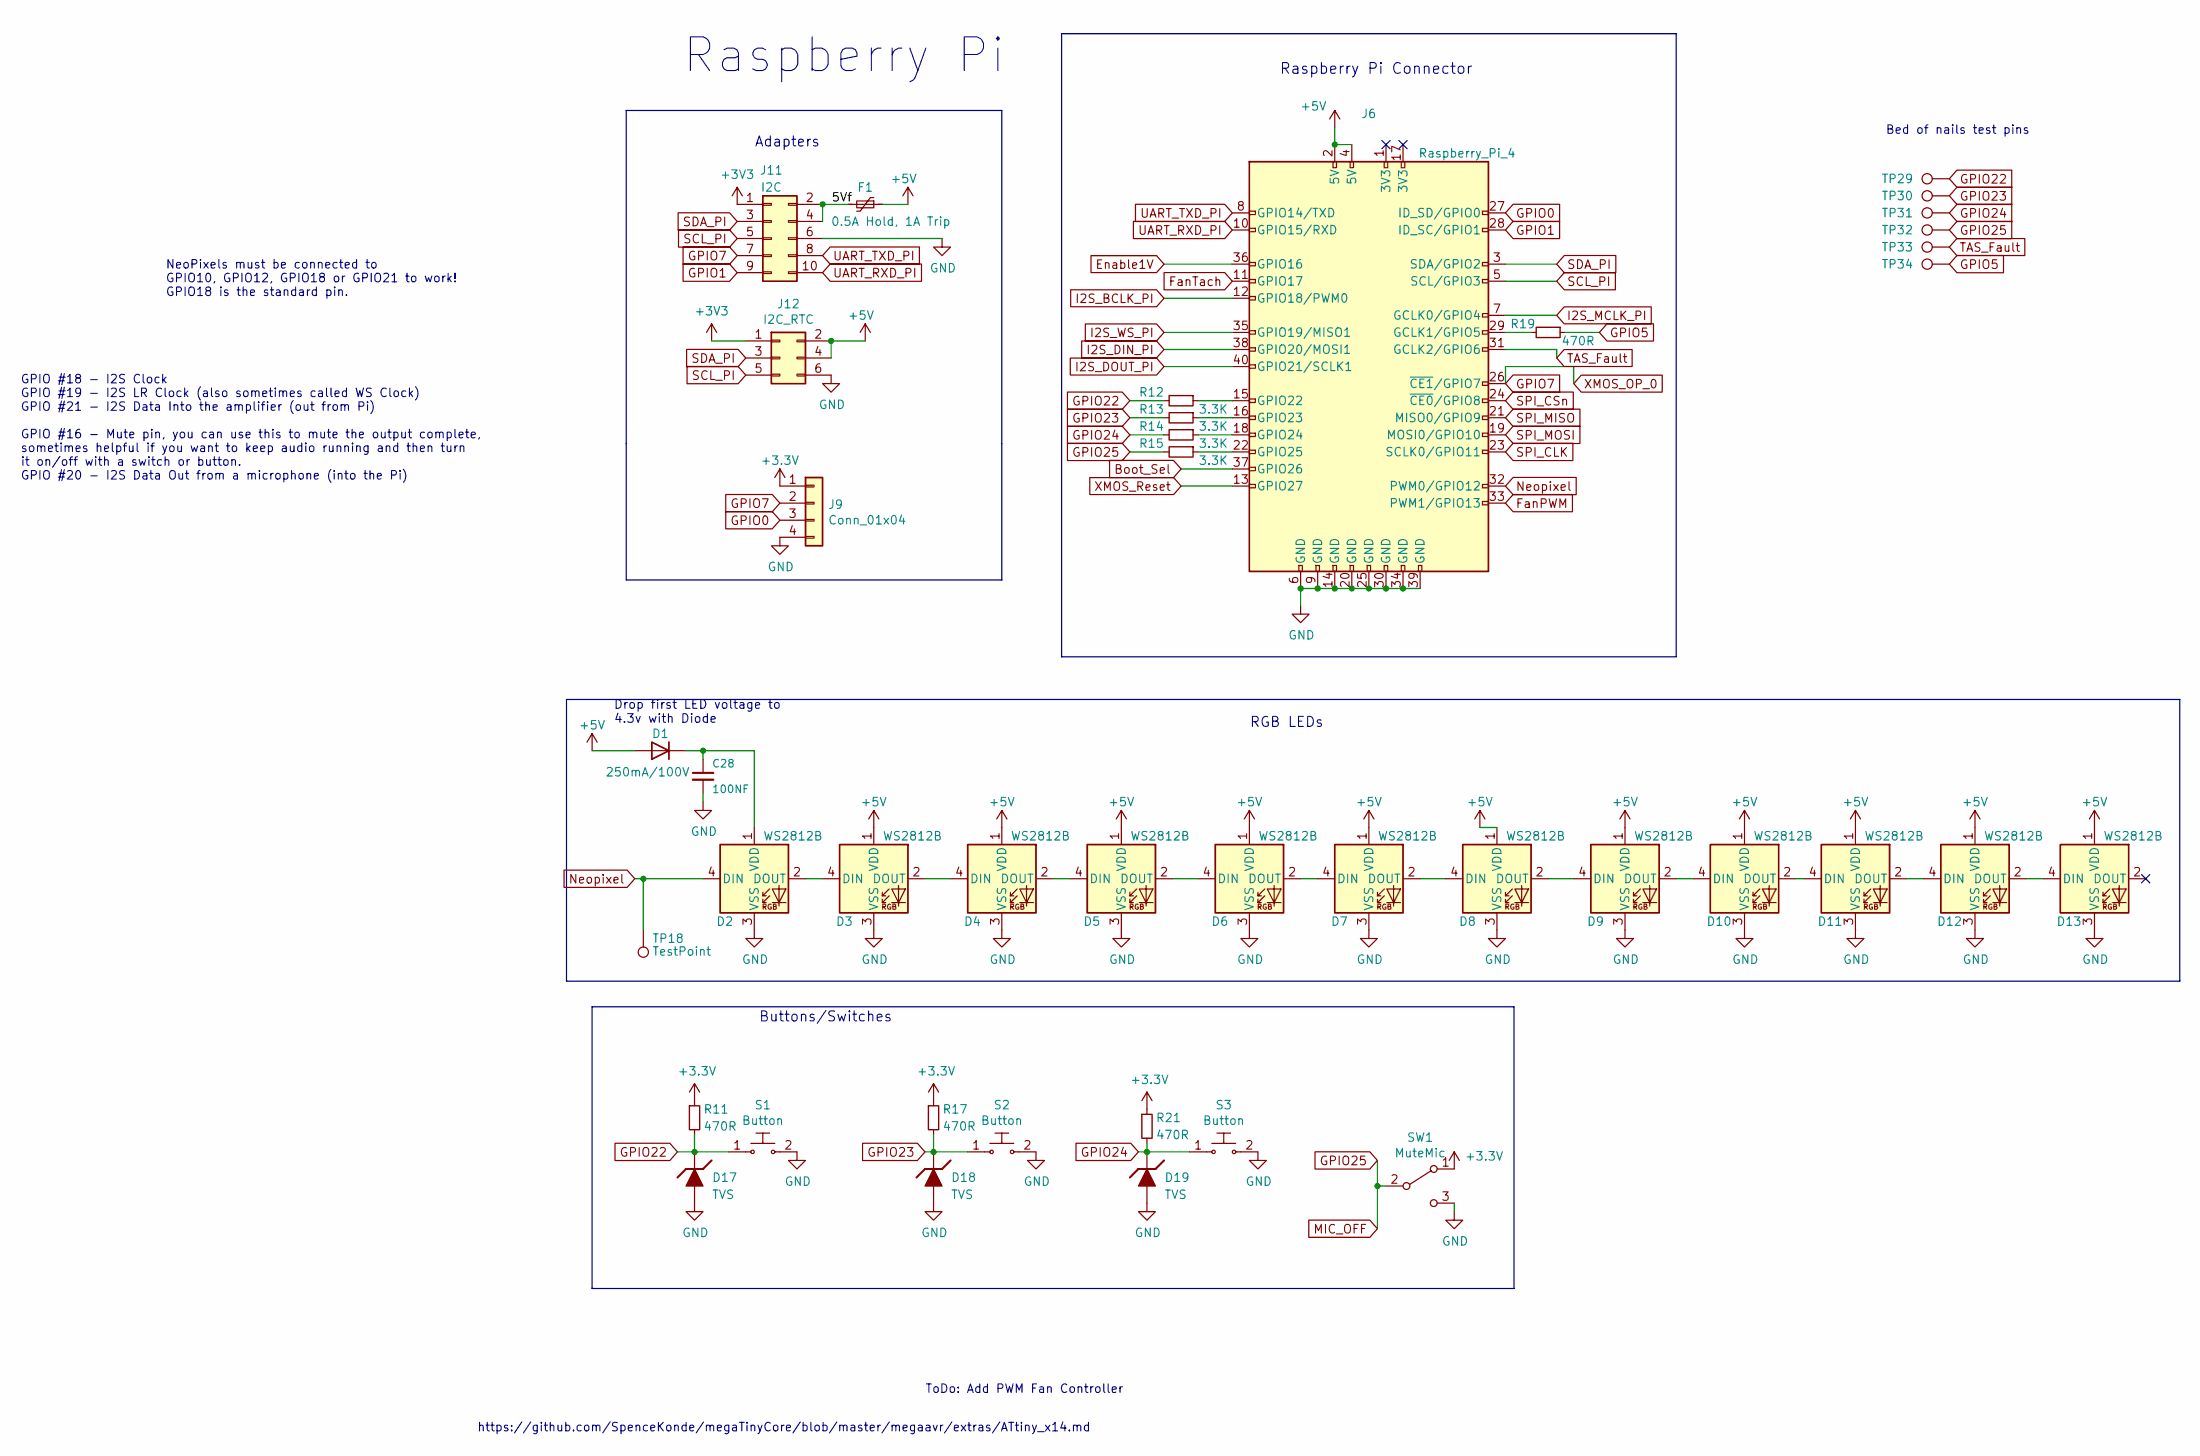
[picture p146: schematic RaspberryPi.kicad_sch]

Parts:
C28: 100NF; C_0402_1005Metric; MPN CC0402KRX7R8BB104; LCSC C1525
D1: 250mA/100V; D_SOD-323F; MPN 1N4148WSF-7; LCSC C2128
D2: WS2812B; LED_WS2812_Mini_3.5x3.5mm_P1.1mm; MPN WS2812B-Mini; LCSC C527089
D3, D4, D5, D6, D7, D8, D9, D10, D11, D12, D13: WS2812B; LED_WS2812_Mini_3.5x3.5mm_P1.1mm; MPN WS2812B-MINI(WS2812B-3535); LCSC C527089
D17, D18, D19: TVS; D_SOD-323; LCSC C139297
F1: 0.5A Hold, 1A Trip; Fuse_1206_3216Metric; LCSC C163512
J6: Raspberry_Pi_4; PinSocket_2x20_P2.54mm_Horizontal; MPN FH412-2*20P 0.8U
J9: Conn_01x04; PinHeader_1x04_P2.54mm_Vertical; MPN DNP
J11: I2C; IDC-Header_2x05_P2.54mm_Horizontal; MPN C9140; LCSC C9140
J12: I2C_RTC; PinHeader_2x03_P2.54mm_Vertical; MPN DNP
R11, R17, R19, R21: 470R; R_0603_1608Metric; MPN 0603WAF4700T5E; LCSC C23179
R12, R13, R14, R15: 3.3K; R_0402_1005Metric; MPN 0402WGF3301TCE; LCSC C25890
S1: Button; SW_SPST_TL3342; MPN TL3342F160QG/TR; Digikey EG2531TR-ND
S2, S3: Button; SW_SPST_TL3342; MPN TL3342F160QG/TR; Digi-Key_PN EG2531TR-ND
SW1: MuteMic; SW_SPDT_PCM12; MPN PCM12SMTR; Digikey 401-2016-2-ND
TP18, TP33, TP34: TestPoint; TestPoint_Pad_D1.0mm; MPN DNP
TP29, TP30, TP31, TP32: TestPoint; TestPoint_Pad_D2.0mm; MPN DNP

Connections:
5Vf: F1.2, J11.2, J11.4
+3.3V: J9.1, R11.1, R17.1, R21.1, SW1.1 (A)
+3V3: J11.1, J12.1
+5V: D1.2 (A), D3.1 (VDD), D4.1 (VDD), D5.1 (VDD), D6.1 (VDD), D7.1 (VDD), D8.1 (VDD), D9.1 (VDD), D10.1 (VDD), D11.1 (VDD), D12.1 (VDD), D13.1 (VDD), F1.1, J6.2 (5V), J6.4 (5V), J12.2, J12.4
Boot_Sel: J6.37 (GPIO26)
Enable1V: J6.36 (GPIO16)
FanPWM: J6.33 (PWM1/GPIO13)
FanTach: J6.11 (GPIO17)
GND: C28.2, D2.3 (VSS), D3.3 (VSS), D4.3 (VSS), D5.3 (VSS), D6.3 (VSS), D7.3 (VSS), D8.3 (VSS), D9.3 (VSS), D10.3 (VSS), D11.3 (VSS), D12.3 (VSS), D13.3 (VSS), D17.2, D18.2, D19.2, J6.6 (GND), J6.9 (GND), J6.14 (GND), J6.20 (GND), J6.25 (GND), J6.30 (GND), J6.34 (GND), J6.39 (GND), J9.4, J11.6, J12.6, S1.2, S2.2, S3.2, SW1.3 (C)
GPIO0: J6.27 (ID_SD/GPIO0), J9.3
GPIO1: J6.28 (ID_SC/GPIO1), J11.9
GPIO5: R19.1, TP34.1
GPIO7: J6.26 (~CE1/GPIO7), J9.2, J11.7
GPIO22: D17.1, R11.2, R12.2, S1.1, TP29.1
GPIO23: D18.1, R13.2, R17.2, S2.1, TP30.1
GPIO24: D19.1, R14.2, R21.2, S3.1, TP31.1
GPIO25: R15.2, SW1.2 (B), TP32.1
I2S_BCLK_PI: J6.12 (GPIO18/PWM0)
I2S_DIN_PI: J6.38 (GPIO20/MOSI1)
I2S_DOUT_PI: J6.40 (GPIO21/SCLK1)
I2S_MCLK_PI: J6.7 (GCLK0/GPIO4)
I2S_WS_PI: J6.35 (GPIO19/MISO1)
Neopixel: D2.4 (DIN), J6.32 (PWM0/GPIO12), TP18.1
unnamed: C28.1, D1.1 (K), D2.1 (VDD)
unnamed: D2.2 (DOUT), D3.4 (DIN)
unnamed: D3.2 (DOUT), D4.4 (DIN)
unnamed: D4.2 (DOUT), D5.4 (DIN)
unnamed: D5.2 (DOUT), D6.4 (DIN)
unnamed: D6.2 (DOUT), D7.4 (DIN)
unnamed: D7.2 (DOUT), D8.4 (DIN)
unnamed: D8.2 (DOUT), D9.4 (DIN)
unnamed: D10.2 (DOUT), D11.4 (DIN)
unnamed: D9.2 (DOUT), D10.4 (DIN)
unnamed: D11.2 (DOUT), D12.4 (DIN)
unnamed: D12.2 (DOUT), D13.4 (DIN)
unnamed: J6.15 (GPIO22), R12.1
unnamed: J6.16 (GPIO23), R13.1
unnamed: J6.18 (GPIO24), R14.1
unnamed: J6.22 (GPIO25), R15.1
unnamed: J6.29 (GCLK1/GPIO5), R19.2
SCL_PI: J6.5 (SCL/GPIO3), J11.5, J12.5
SDA_PI: J6.3 (SDA/GPIO2), J11.3, J12.3
SPI_CLK: J6.23 (SCLK0/GPIO11)
SPI_CSn: J6.24 (~CE0/GPIO8)
SPI_MISO: J6.21 (MISO0/GPIO9)
SPI_MOSI: J6.19 (MOSI0/GPIO10)
TAS_Fault: J6.31 (GCLK2/GPIO6), TP33.1
UART_RXD_PI: J6.10 (GPIO15/RXD), J11.10
UART_TXD_PI: J6.8 (GPIO14/TXD), J11.8
XMOS_Reset: J6.13 (GPIO27)

Notes on the sheet:
NeoPixels must be connected to GPIO10, GPIO12, GPIO18 or GPIO21 to work! GPIO18 is the standard pin.
Raspberry Pi
Adapters
Raspberry Pi Connector
RGB LEDs
GPIO #18 - I2S Clock GPIO #19 - I2S LR Clock (also sometimes called WS Clock) GPIO #21 - I2S Data Into the amplifier (out from Pi) GPIO #16 - Mute pin, you can use this to mute the output complete, sometimes helpful if you want to keep audio running and then turn it on/off with a switch or button. 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
ToDo: Add PWM Fan Controller
https://github.com/SpenceKonde/megaTinyCore/blob/master/megaavr/extras/ATtiny_x14.md
Bed of nails test pins
Buttons/Switches
Drop first LED voltage to 4.3v with Diode
