MycroftAI/hardware-mycroft-mark-II/mark-II-production/SJ-201-R10.kicad_sch

## KiCad design mark-II-production/SJ-201-R10.kicad_sch (2022-10-22)

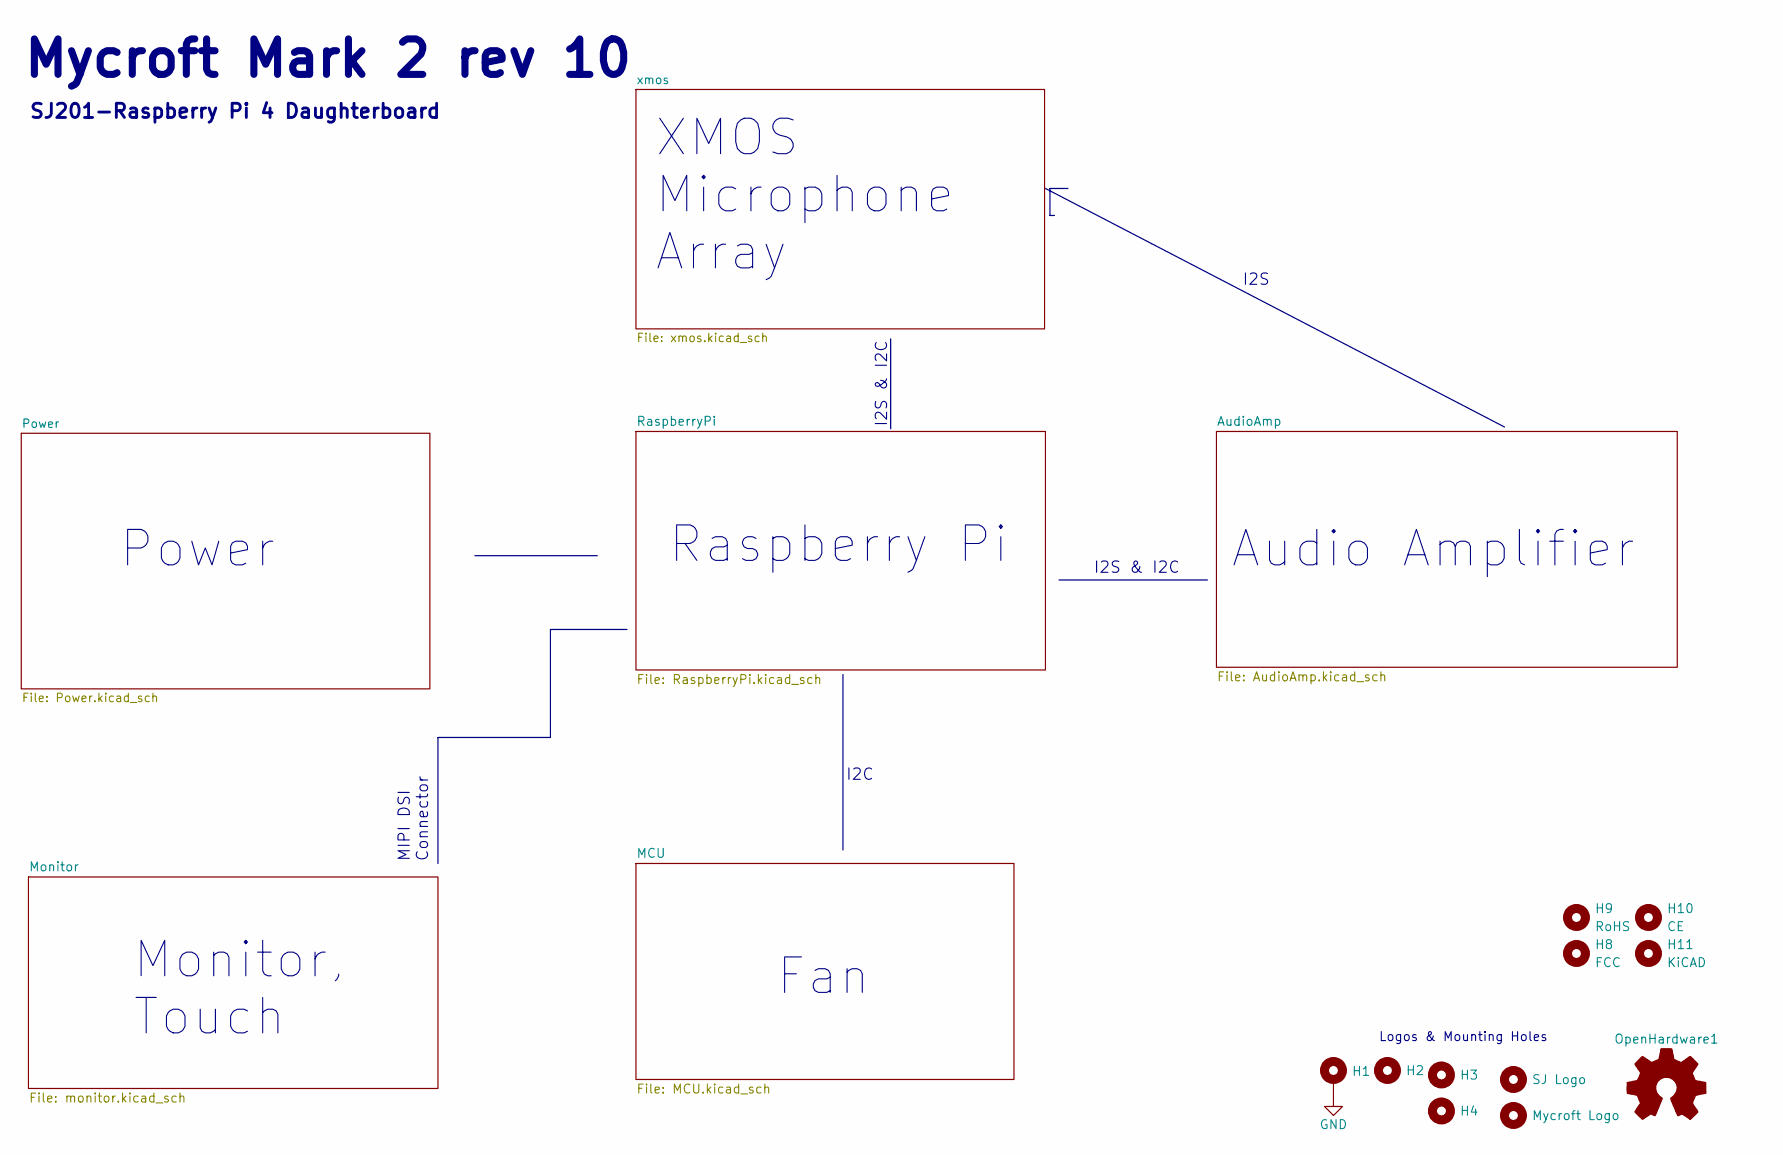
[picture p147: schematic SJ-201-R10.kicad_sch]

Parts:
H1, H3, H4: MountingHole; MountingHole_6.0mm_Pad; MPN DNP
H2: MountingHole; MountingHole_6.5mm_Pad; MPN DNP
H6: SJ Logo; simon-jestor-logo; MPN DNP
H7: Mycroft Logo; mycroft_logo_words; MPN DNP
H8: FCC; FCC-Logo_7.3x6mm_SilkScreen; MPN DNP
H9: RoHS; RoHS-Logo_6mm_SilkScreen; MPN DNP
H10: CE; CE-Logo_8.5x6mm_SilkScreen; MPN DNP
H11: KiCAD; KiCad-Logo2_5mm_SilkScreen; MPN DNP
OpenHardware1: Logo_Open_Hardware_Small; OSHW-Logo_7.5x8mm_SilkScreen; MPN DNP

Connections:
GND: H1.1

Notes on the sheet:
I2S
SJ201-Raspberry Pi 4 Daughterboard
Mycroft Mark 2 rev 10
MIPI DSI Connector
Monitor, Touch
Raspberry Pi
Logos & Mounting Holes
Fan
I2S & I2C
Power
XMOS Microphone Array
Audio Amplifier
I2C
