MycroftAI/hardware-mycroft-mark-II/mark-II-production/xmos.kicad_sch

## KiCad design mark-II-production/xmos.kicad_sch (2022-10-22)

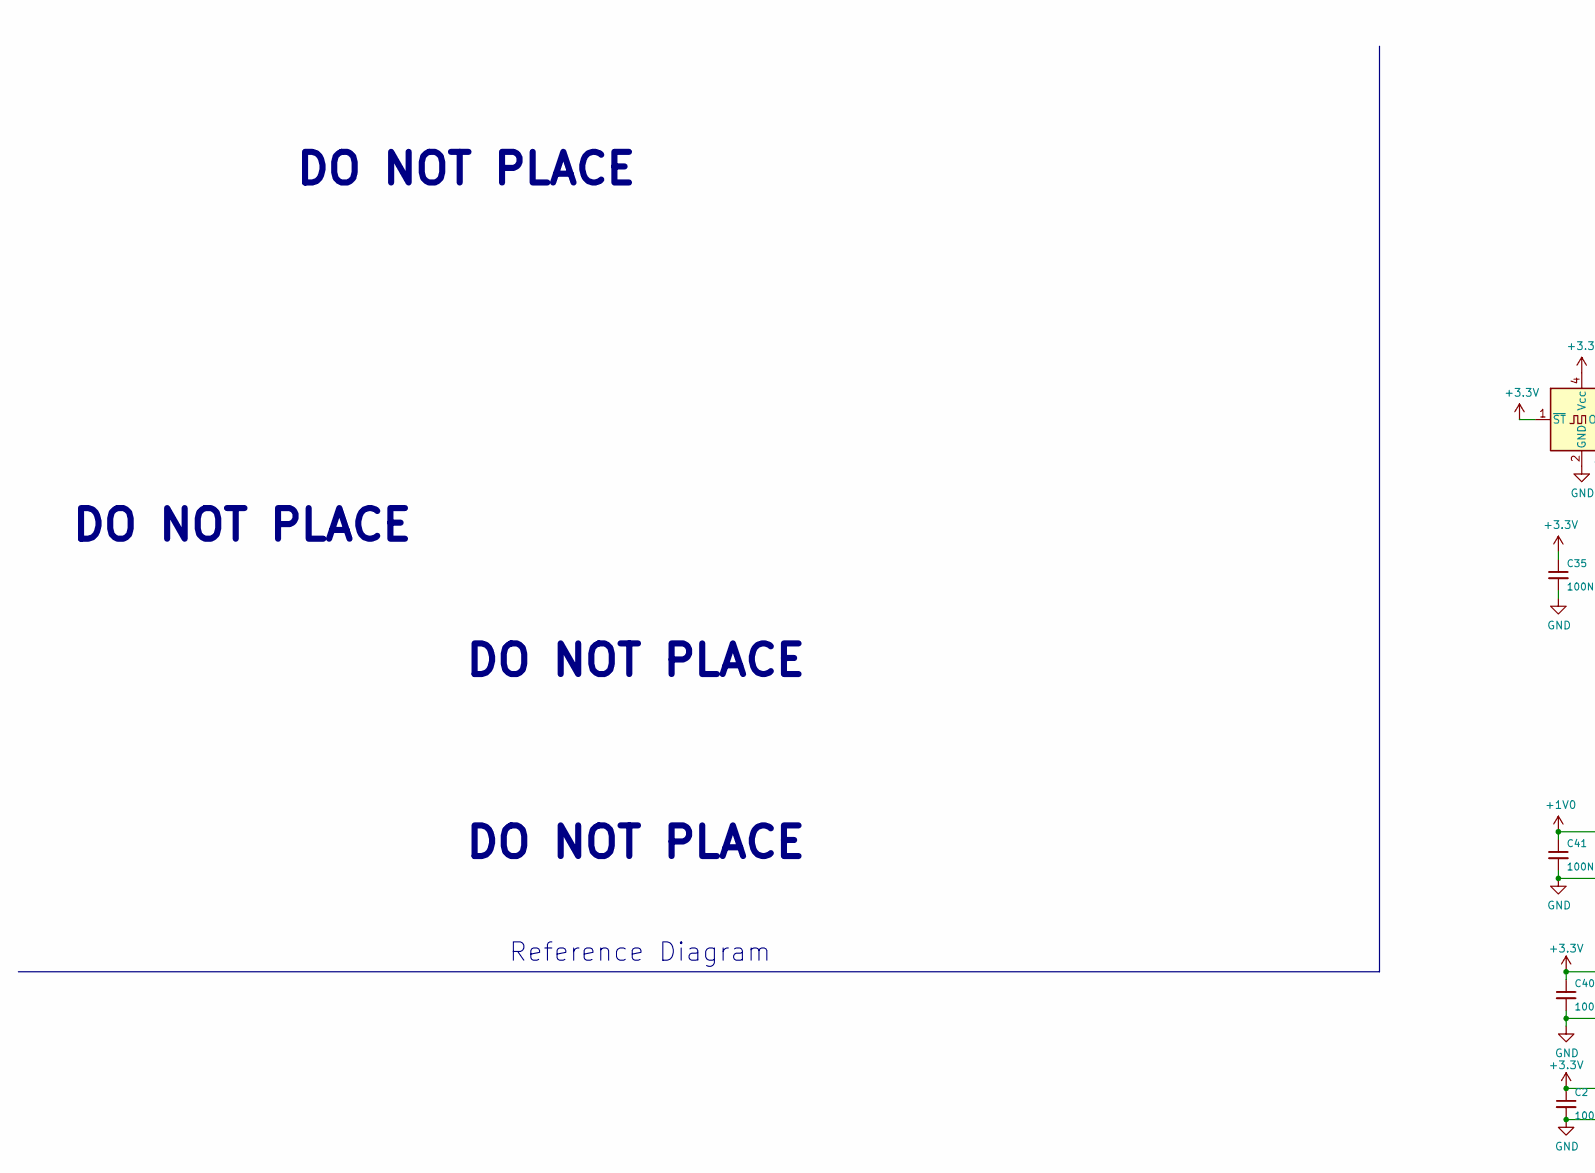
[picture p148: schematic xmos.kicad_sch, part in row 1, column 1]

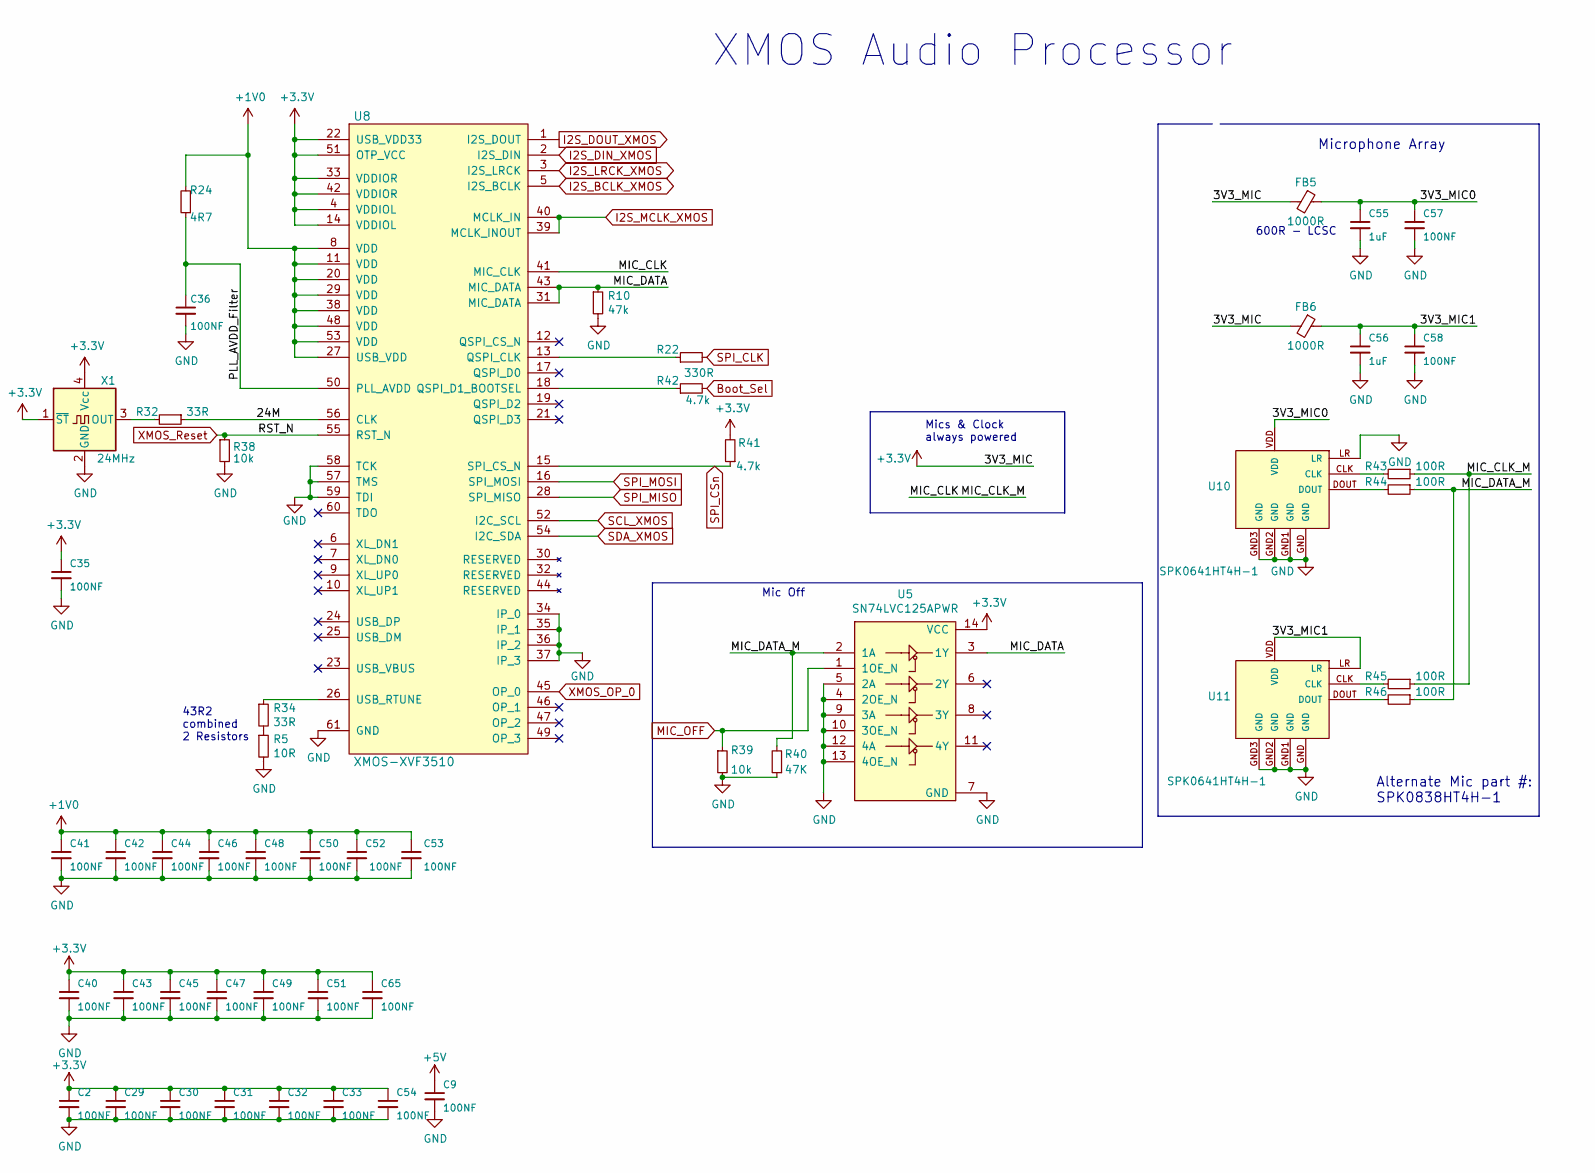
[picture p149: schematic xmos.kicad_sch, part in row 1, column 2]

Parts:
C2, C9, C29, C30, C31, C32, C33, C35, C36, C40, C41, C42, C43, C44, C45, C46, C47, C48, C49, C50, C51, C52, C53, C54, C57, C58, C65: 100NF; C_0402_1005Metric; MPN CC0402KRX7R8BB104; LCSC C1525
C55, C56: 1uF; C_0402_1005Metric; MPN CL05A105KA5NQNC; LCSC C52923
FB5: 1000R; R_0805_2012Metric; MPN MPZ1608S102ATA00; LCSC C1017
FB6: 1000R; R_0805_2012Metric; PartNum MPZ1608S102ATA00; LCSC C1017
R5: 10R; R_0402_1005Metric; MPN 0402WGF100JTCE; LCSC C25077
R10: 47k; R_0402_1005Metric; MPN 0402WGF4702TCE; LCSC C25792
R22: 330R; R_0402_1005Metric; MPN RC0402FR-07330RL; LCSC C25104
R24: 4R7; R_0603_1608Metric; MPN RC0402FR-074R7L; LCSC C23164
R32, R34: 33R; R_0402_1005Metric; MPN 0402WGF330JTCE; LCSC C25105
R38, R39: 10k; R_0402_1005Metric; MPN RC0402FR-0710KL; LCSC C25744
R40: 47K; R_0402_1005Metric; MPN RC0402JR-0747KL; LCSC C25792
R41, R42: 4.7k; R_0402_1005Metric; MPN 0402WGF4701TCE; LCSC C25900
R43, R44, R45, R46: 100R; R_0402_1005Metric; MPN 0402WGF1000TCE; LCSC C25076
U5: SN74LVC125APWR; TSSOP-14_4.4x5mm_P0.65mm; MPN SN74LVC125APWR; LCSC C7813
U8: XMOS-XVF3510; QFN-60-1EP_7x7mm_P0.4mm_EP5.6x5.6mm; MPN XVF3510-QF60-C
U10, U11: SPK0641HT4H-1; HCLGA-MP34DT05; MPN SPK0641HT4H-1; Digikey 423-1425-1-ND
X1: 24MHz; Oscillator_SMD_SeikoEpson_SG210-4Pin_2.5x2.0mm; MPN 2N24000G33YC; LCSC C252326

Connections:
3V3_MIC0: C55.1, C57.1, FB5.1, U10.VDD
3V3_MIC1: C56.1, C58.1, FB6.1, U11.LR, U11.VDD
24M: R32.1, U8.56 (CLK)
+1V0: C41.1, C42.1, C44.1, C46.1, C48.1, C50.1, C52.1, C53.1, R24.2, U8.8 (VDD), U8.11 (VDD), U8.20 (VDD), U8.27 (USB_VDD), U8.29 (VDD), U8.38 (VDD), U8.48 (VDD), U8.53 (VDD)
+3.3V: C2.1, C29.1, C30.1, C31.1, C32.1, C33.1, C35.1, C40.1, C43.1, C45.1, C47.1, C49.1, C51.1, C54.1, C65.1, FB5.2, FB6.2, R41.2, U5.14 (VCC), U8.4 (VDDIOL), U8.14 (VDDIOL), U8.22 (USB_VDD33), U8.33 (VDDIOR), U8.42 (VDDIOR), U8.51 (OTP_VCC), X1.1 (~ST), X1.4 (Vcc)
+5V: C9.1
Boot_Sel: R42.2
GND: C2.2, C9.2, C29.2, C30.2, C31.2, C32.2, C33.2, C35.2, C36.2, C40.2, C41.2, C42.2, C43.2, C44.2, C45.2, C46.2, C47.2, C48.2, C49.2, C50.2, C51.2, C52.2, C53.2, C54.2, C55.2, C56.2, C57.2, C58.2, C65.2, R5.2, R10.2, R38.2, R39.2, R40.1, U5.4 (2OE_N), U5.5 (2A), U5.7 (GND), U5.9 (3A), U5.10 (3OE_N), U5.12 (4A), U5.13 (4OE_N), U8.34 (IP_0), U8.35 (IP_1), U8.36 (IP_2), U8.37 (IP_3), U8.57 (TMS), U8.58 (TCK), U8.59 (TDI), U8.61 (GND), U10.GND, U10.GND1 (GND), U10.GND2 (GND), U10.GND3 (GND), U10.LR, U11.GND, U11.GND1 (GND), U11.GND2 (GND), U11.GND3 (GND), X1.2 (GND)
I2S_BCLK_XMOS: U8.5 (I2S_BCLK)
I2S_DIN_XMOS: U8.2 (I2S_DIN)
I2S_DOUT_XMOS: U8.1 (I2S_DOUT)
I2S_LRCK_XMOS: U8.3 (I2S_LRCK)
I2S_MCLK_XMOS: U8.39 (MCLK_INOUT), U8.40 (MCLK_IN)
MIC_CLK: R43.1, R45.1, U8.41 (MIC_CLK)
MIC_DATA: R10.1, U5.3 (1Y), U8.31 (MIC_DATA), U8.43 (MIC_DATA)
MIC_DATA_M: R40.2, R44.1, R46.1, U5.2 (1A)
MIC_OFF: R39.1, U5.1 (1OE_N)
unnamed: R22.1, U8.13 (QSPI_CLK)
unnamed: R32.2, X1.3 (OUT)
unnamed: R34.1, U8.26 (USB_RTUNE)
unnamed: R5.1, R34.2
unnamed: R42.1, U8.18 (QSPI_D1_BOOTSEL)
unnamed: R43.2, U10.CLK
unnamed: R44.2, U10.DOUT
unnamed: R45.2, U11.CLK
unnamed: R46.2, U11.DOUT
PLL_AVDD_Filter: C36.1, R24.1, U8.50 (PLL_AVDD)
SCL_XMOS: U8.52 (I2C_SCL)
SDA_XMOS: U8.54 (I2C_SDA)
SPI_CLK: R22.2
SPI_CSn: R41.1, U8.15 (SPI_CS_N)
SPI_MISO: U8.28 (SPI_MISO)
SPI_MOSI: U8.16 (SPI_MOSI)
XMOS_OP_0: U8.45 (OP_0)
XMOS_Reset: R38.1, U8.55 (RST_N)

Notes on the sheet:
Mic Off
43R2 combined 2 Resistors
600R - LCSC
Alternate Mic part #: SPK0838HT4H-1
XMOS Audio Processor
DO NOT PLACE
Mics & Clock always powered
Reference Diagram
Microphone Array
